franrobots/RescueMaze_FranRobots_National2024/Mechanics/MAZE ROBOT 2024/Extras/Render/Renders antigas/Configurações Render.jpg

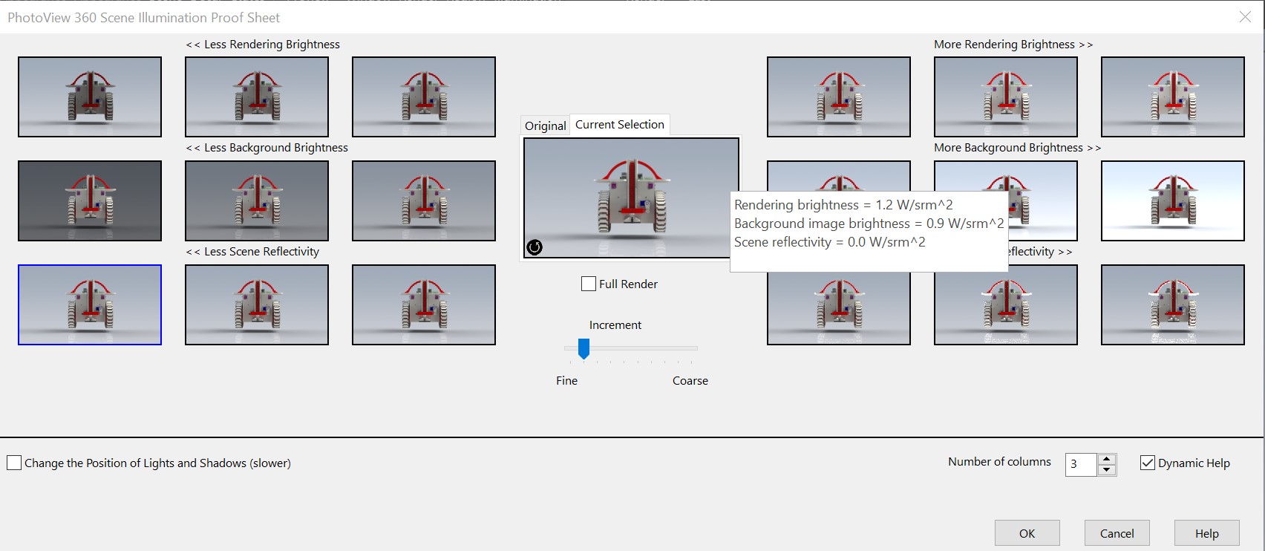
Mechanics/MAZE ROBOT 2024/Extras/Render/Renders antigas/Configurações Render.jpg
