franrobots/RescueMaze_FranRobots_National2024/Programming/Media/Flowcharts/Fluxograma Botão de Interrupção.png

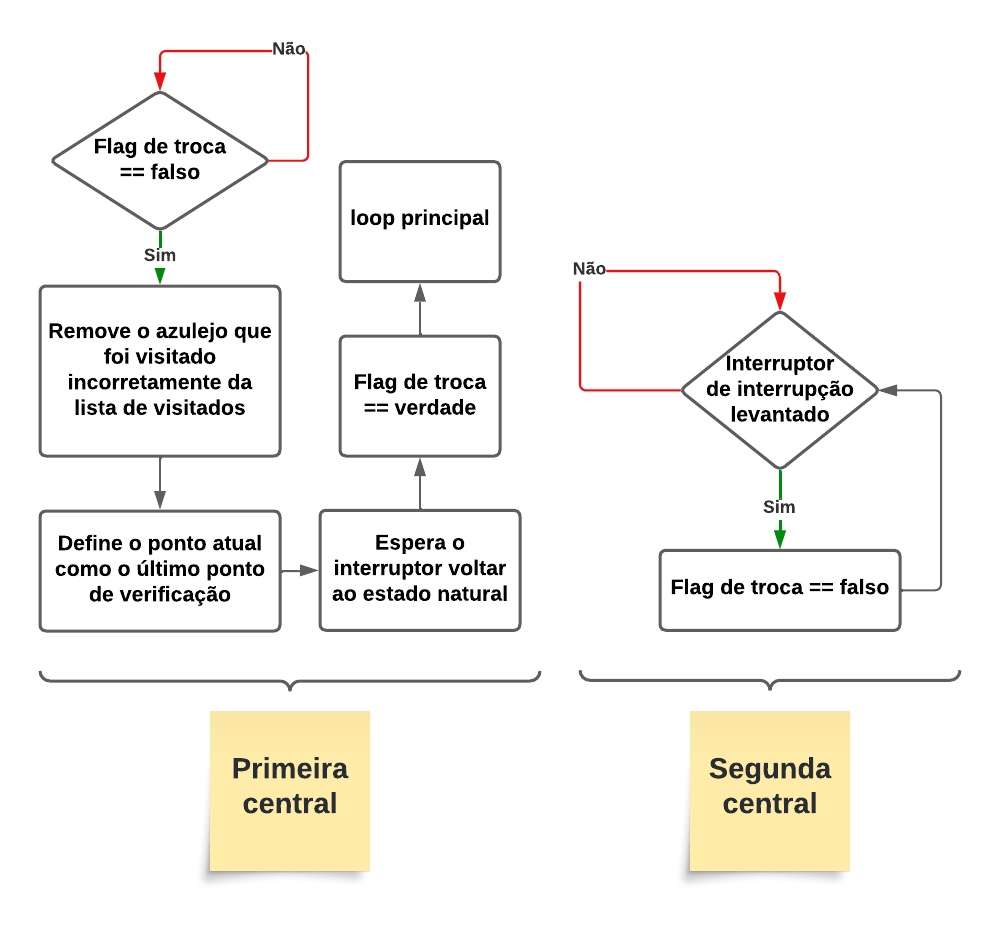
Programming/Media/Flowcharts/Fluxograma Botão de Interrupção.png
