franrobots/RescueMaze_FranRobots_National2024/Programming/Media/Flowcharts/Fluxograma Decisões do Robô.png

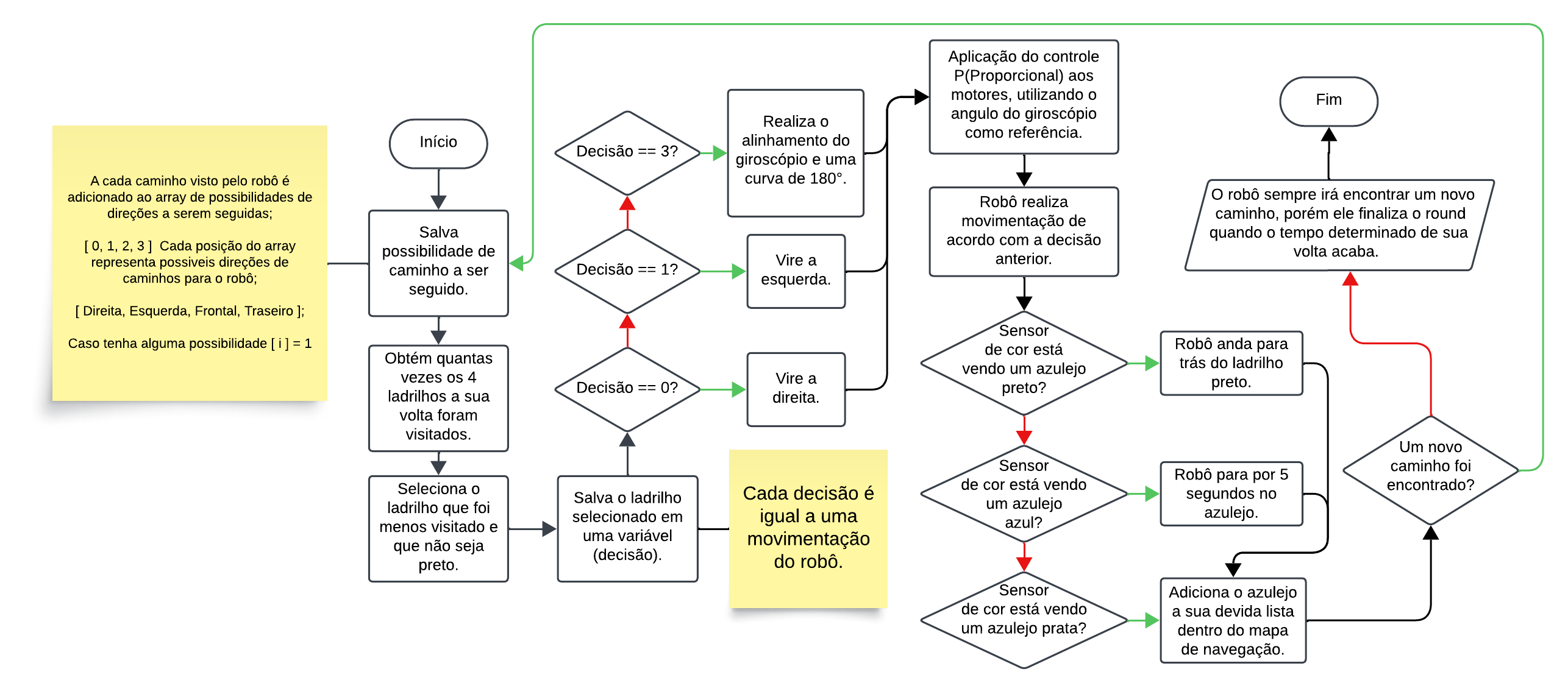
Programming/Media/Flowcharts/Fluxograma Decisões do Robô.png
