franrobots/RescueMaze_FranRobots_National2024/Programming/Media/Flowcharts/Fluxograma Identificação de Imagem.png

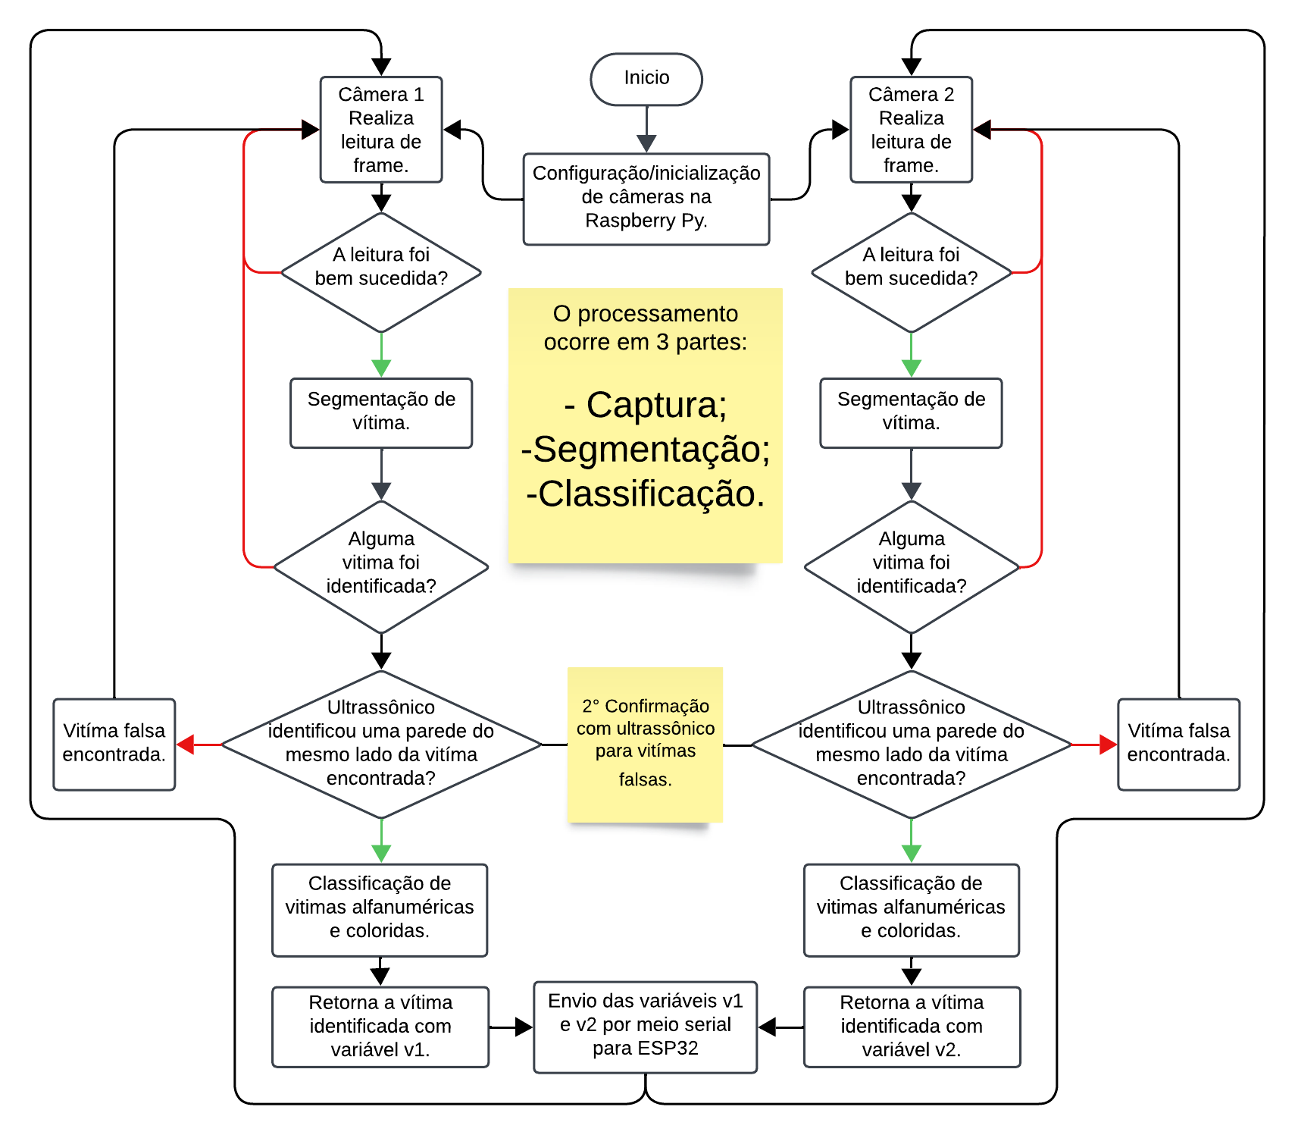
Programming/Media/Flowcharts/Fluxograma Identificação de Imagem.png
