franrobots/RescueMaze_FranRobots_National2024/Programming/Media/Flowcharts/Fluxograma Ladrilhos Coloridos.png

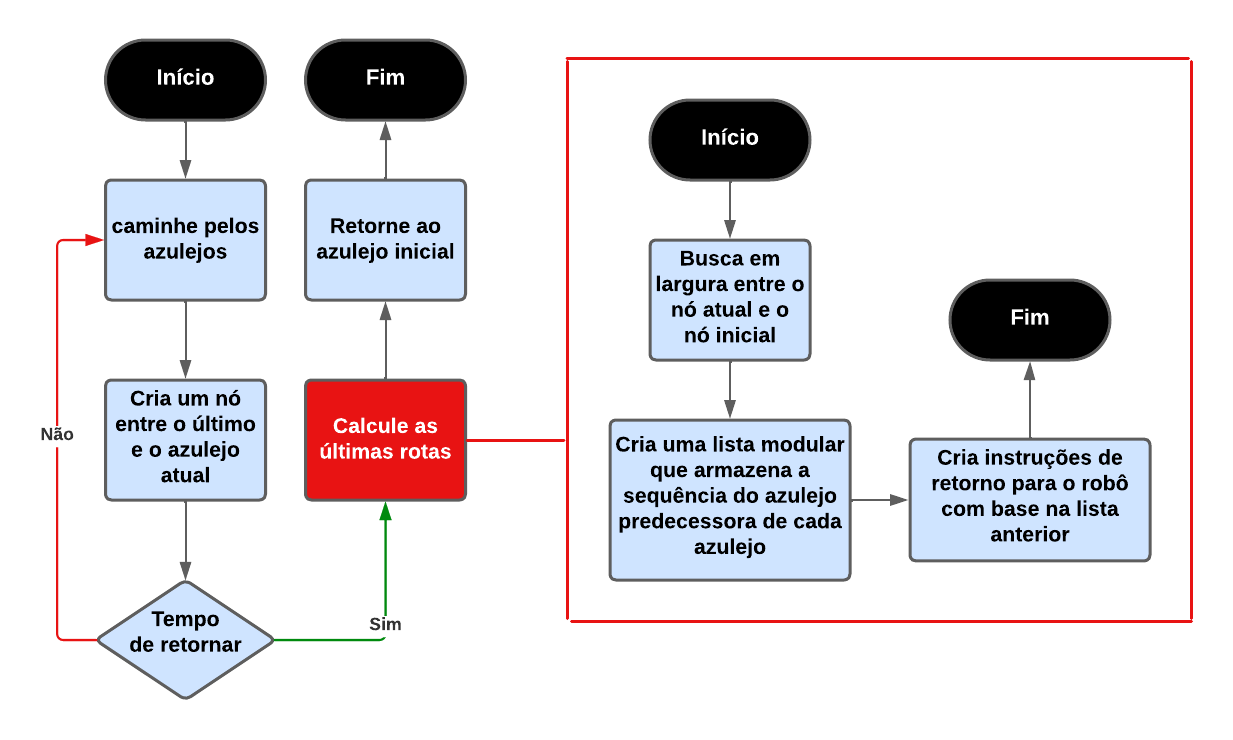
Programming/Media/Flowcharts/Fluxograma Ladrilhos Coloridos.png
