franrobots/RescueMaze_FranRobots_National2024/Programming/Media/Flowcharts/Fluxograma LDR.png

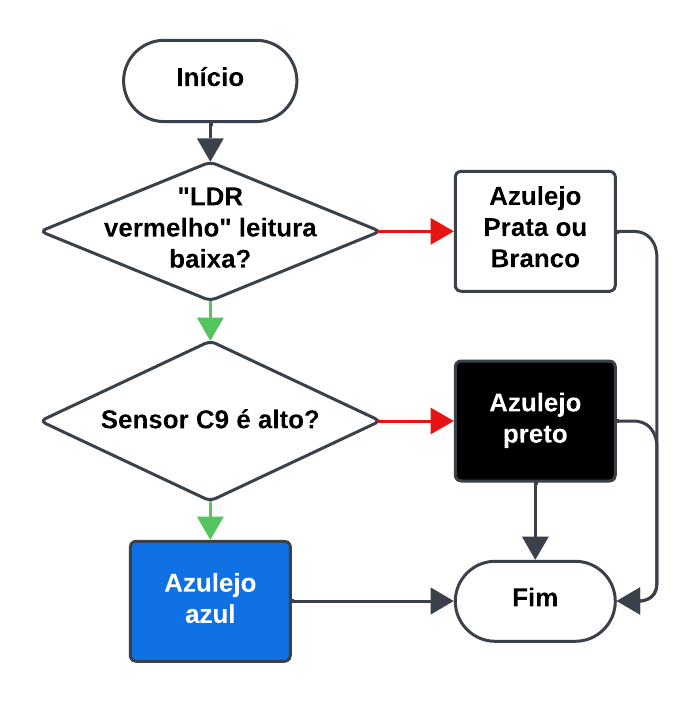
Programming/Media/Flowcharts/Fluxograma LDR.png
