franrobots/RescueMaze_FranRobots_National2024/Programming/Media/Flowcharts/Fluxograma Rotas.png

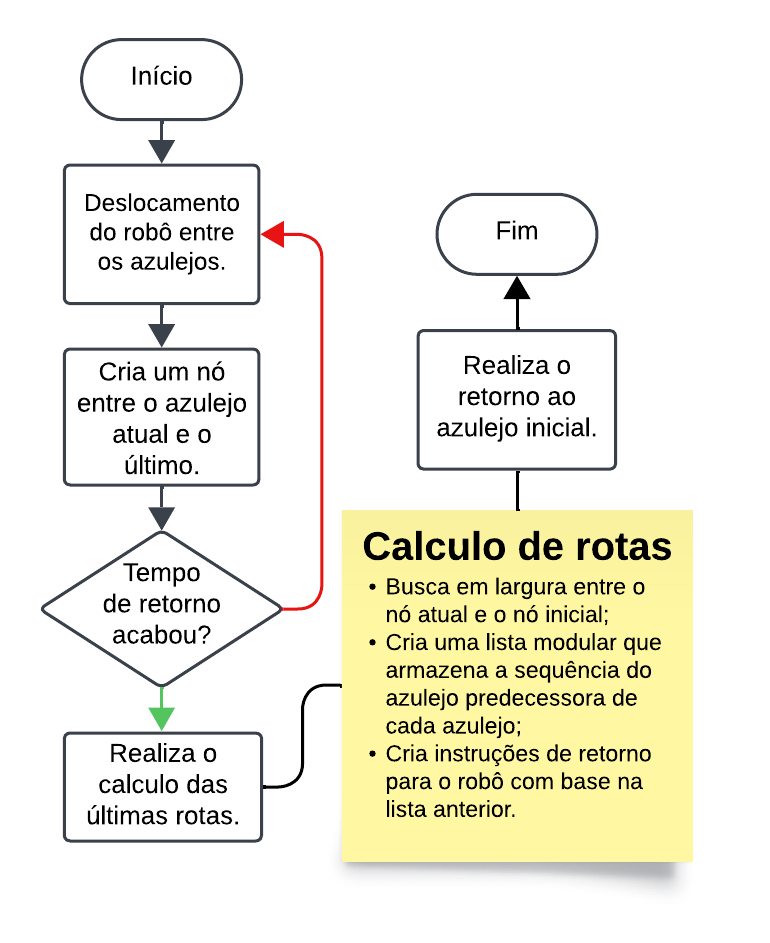
Programming/Media/Flowcharts/Fluxograma Rotas.png
