franrobots/RescueMaze_FranRobots_National2024/Mechanics/MAZE ROBOT 2024/Componentes/Micro-controladoras/RaspberryPi Zero/RaspberryPiZeroW.SLDPRT

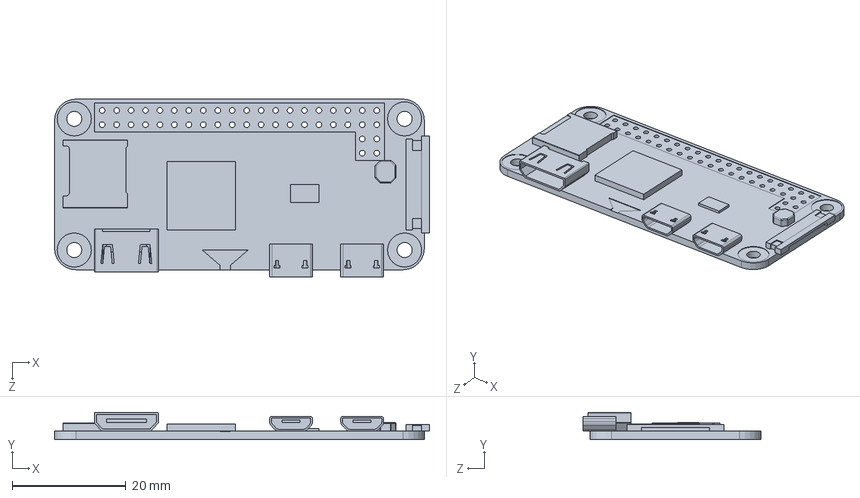
[picture p37: CAD file, 2024-10-25]
Mechanics/MAZE ROBOT 2024/Componentes/Micro-controladoras/RaspberryPi Zero/RaspberryPiZeroW.SLDPRT
65.9 x 4.80 x 31.2 mm
