franrobots/RescueMaze_FranRobots_National2024/Mechanics/MAZE ROBOT 2024/Componentes/Motor DC - MJ TEK8 - 12v 100 RPM.SLDPRT

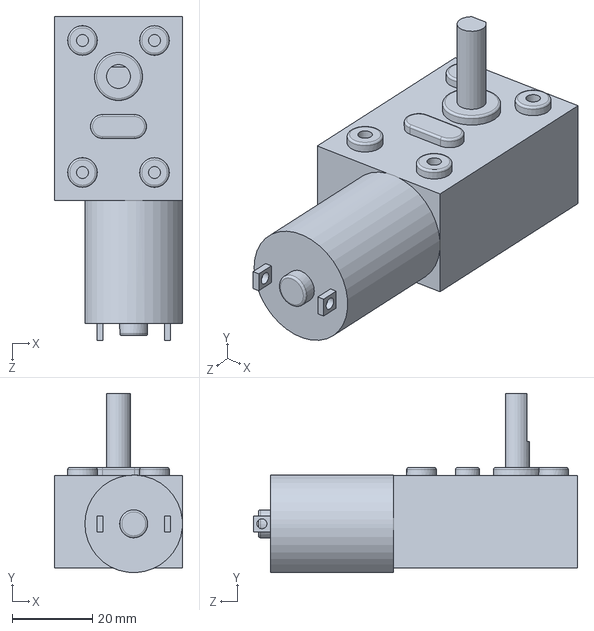
[picture p38: CAD file, 2024-10-25]
Mechanics/MAZE ROBOT 2024/Componentes/Motor DC - MJ TEK8 - 12v 100 RPM.SLDPRT
32.0 x 44.8 x 81.0 mm
