franrobots/RescueMaze_FranRobots_National2024/Mechanics/MAZE ROBOT 2024/Componentes/Parafusos e Porcas/Arruelas/Arruela M3.SLDPRT

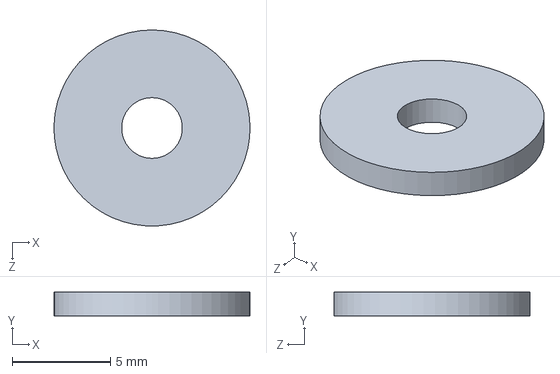
[picture p39: CAD file, 2024-10-25]
Mechanics/MAZE ROBOT 2024/Componentes/Parafusos e Porcas/Arruelas/Arruela M3.SLDPRT
10.00 x 1.20 x 10.0 mm
