franrobots/RescueMaze_FranRobots_National2024/Mechanics/MAZE ROBOT 2024/Componentes/Parafusos e Porcas/Parafusos/Parafuso M3 Liso.SLDPRT

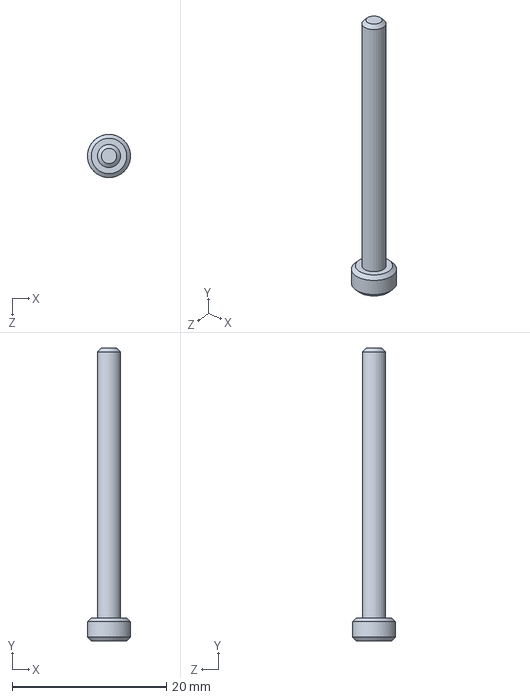
[picture p40: CAD file, 2024-10-25]
Mechanics/MAZE ROBOT 2024/Componentes/Parafusos e Porcas/Parafusos/Parafuso M3 Liso.SLDPRT
5.59 x 38.0 x 5.60 mm
