franrobots/RescueMaze_FranRobots_National2024/Mechanics/MAZE ROBOT 2024/Componentes/Parafusos e Porcas/Porcas/Porca M3.STEP

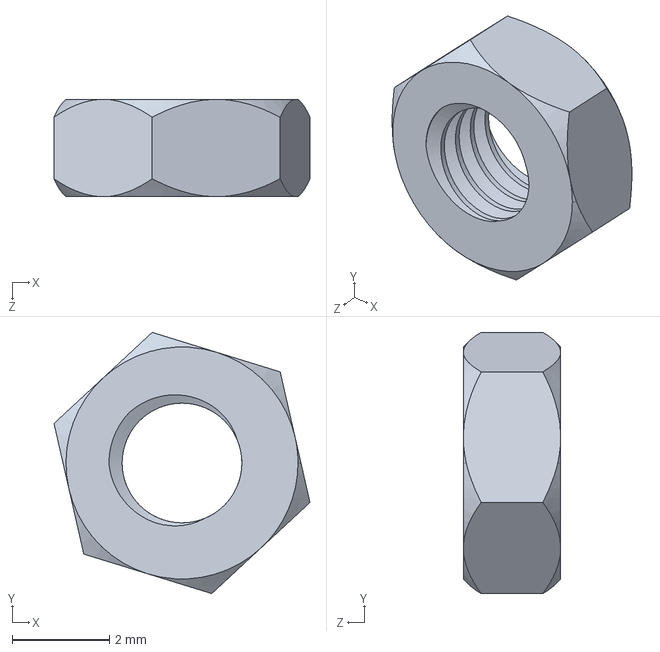
[picture p41: CAD file, 2024-10-25]
Mechanics/MAZE ROBOT 2024/Componentes/Parafusos e Porcas/Porcas/Porca M3.STEP
5.26 x 5.36 x 2.00 mm
