franrobots/RescueMaze_FranRobots_National2024/Mechanics/MAZE ROBOT 2024/Componentes/Placa de Refletância/Case LDR Tripla.SLDPRT

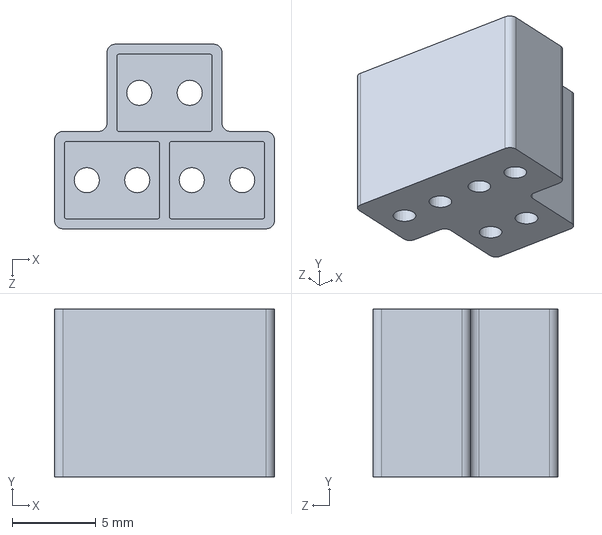
[picture p42: CAD file, 2024-10-25]
Mechanics/MAZE ROBOT 2024/Componentes/Placa de Refletância/Case LDR Tripla.SLDPRT
13.1 x 10.0 x 11.0 mm
