franrobots/RescueMaze_FranRobots_National2024/Mechanics/MAZE ROBOT 2024/Componentes/Placa Mãe - Robô Maze/Conectores/Bornes/2 PIN - DG306-5 - PITCH 5 mm.stp

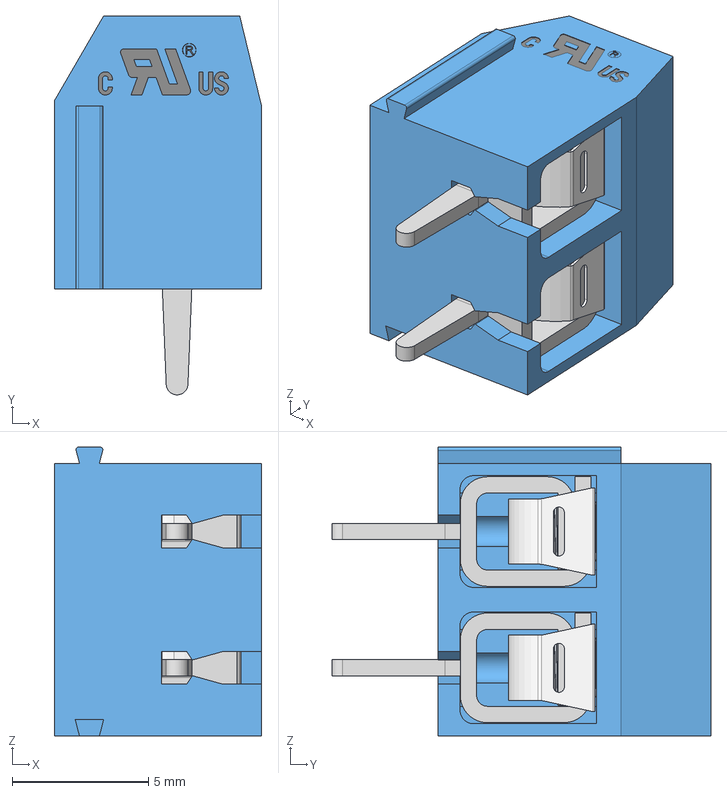
[picture p46: CAD file, 2024-10-25]
Mechanics/MAZE ROBOT 2024/Componentes/Placa Mãe - Robô Maze/Conectores/Bornes/2 PIN - DG306-5 - PITCH 5 mm.stp
7.60 x 13.9 x 10.6 mm
