franrobots/RescueMaze_FranRobots_National2024/Mechanics/MAZE ROBOT 2024/Componentes/Placa Mãe - Robô Maze/Placa Ilhada 90x70.SLDPRT

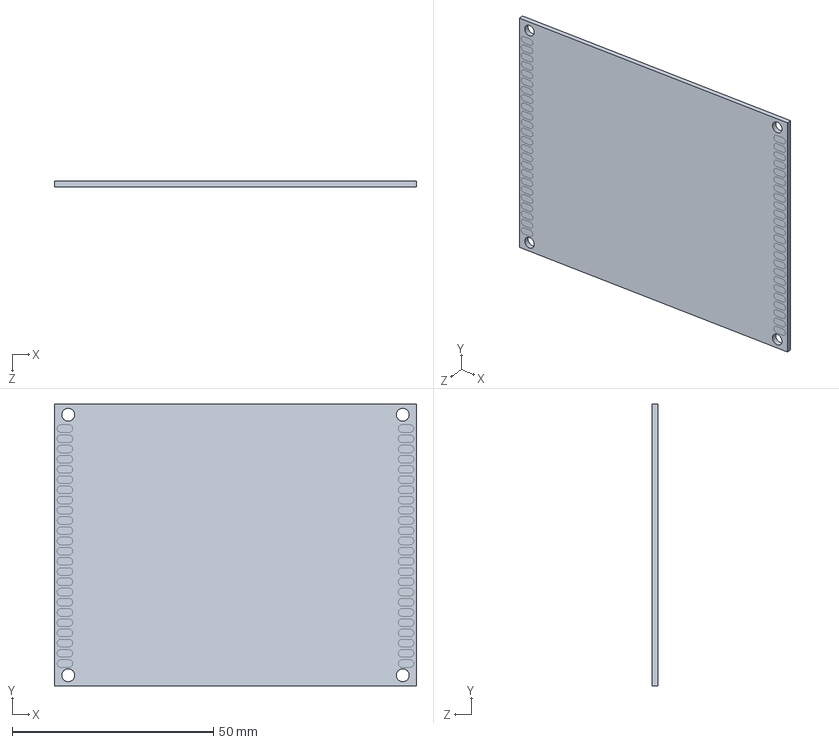
[picture p47: CAD file, 2024-10-25]
Mechanics/MAZE ROBOT 2024/Componentes/Placa Mãe - Robô Maze/Placa Ilhada 90x70.SLDPRT
90.0 x 70.0 x 1.42 mm
