franrobots/RescueMaze_FranRobots_National2024/Mechanics/MAZE ROBOT 2024/Componentes/Servo Motor/Servo Emax ES08A.SLDPRT

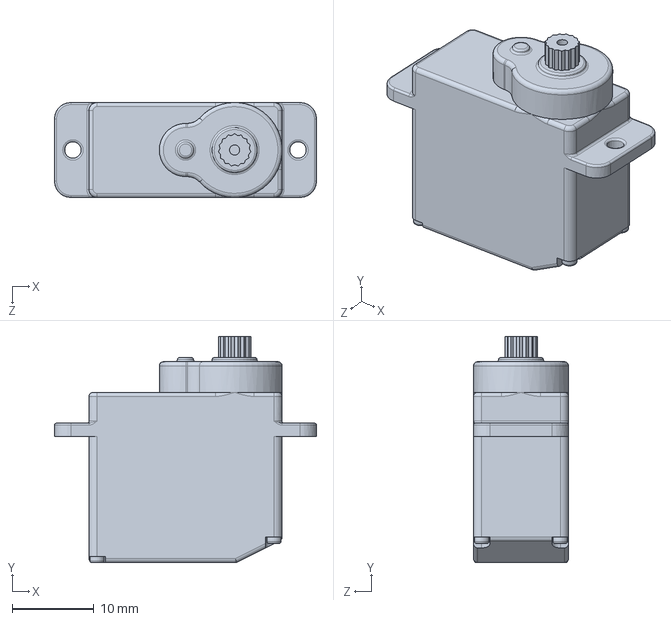
[picture p48: CAD file, 2024-10-25]
Mechanics/MAZE ROBOT 2024/Componentes/Servo Motor/Servo Emax ES08A.SLDPRT
32.0 x 27.6 x 11.6 mm
