franrobots/RescueMaze_FranRobots_National2024/Mechanics/MAZE ROBOT 2024/Componentes/Switchs/3D/Suporte Switch.SLDPRT

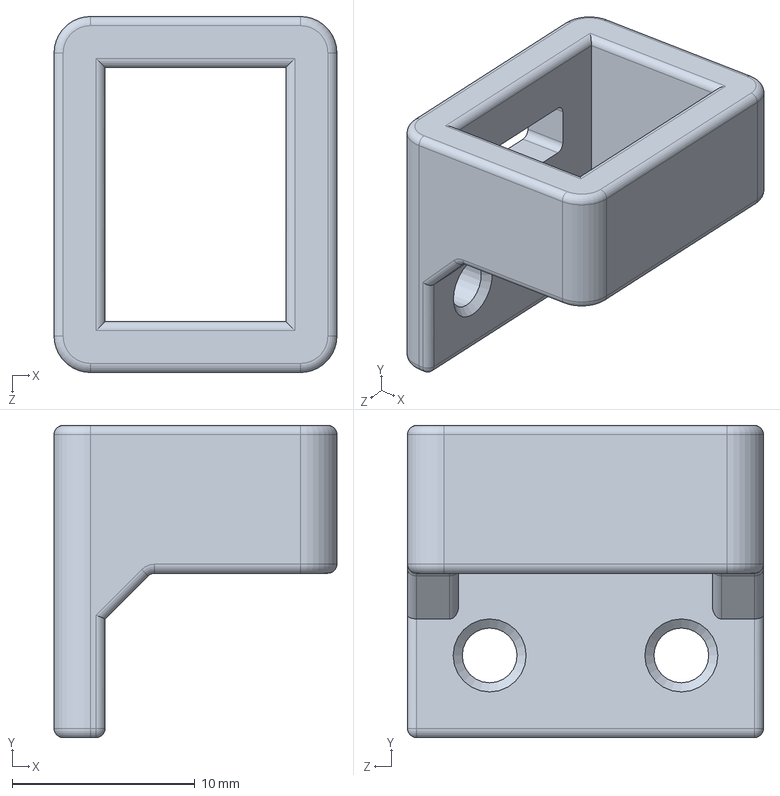
[picture p49: CAD file, 2024-10-25]
Mechanics/MAZE ROBOT 2024/Componentes/Switchs/3D/Suporte Switch.SLDPRT
15.5 x 17.1 x 19.5 mm
