franrobots/RescueMaze_FranRobots_National2024/Mechanics/MAZE ROBOT 2024/Componentes/Switchs/tugas uts rocker switch.SLDPRT

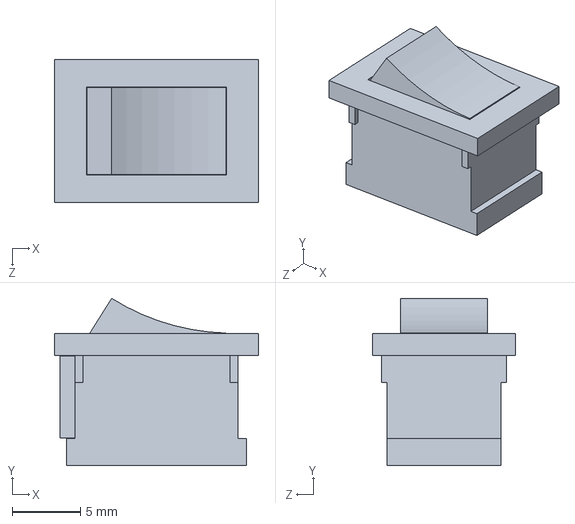
[picture p50: CAD file, 2024-10-25]
Mechanics/MAZE ROBOT 2024/Componentes/Switchs/tugas uts rocker switch.SLDPRT
15.0 x 12.3 x 10.5 mm
