franrobots/RescueMaze_FranRobots_National2024/Mechanics/MAZE ROBOT 2024/Componentes/Ultrassonico/Suporte Ultrassonico.SLDPRT

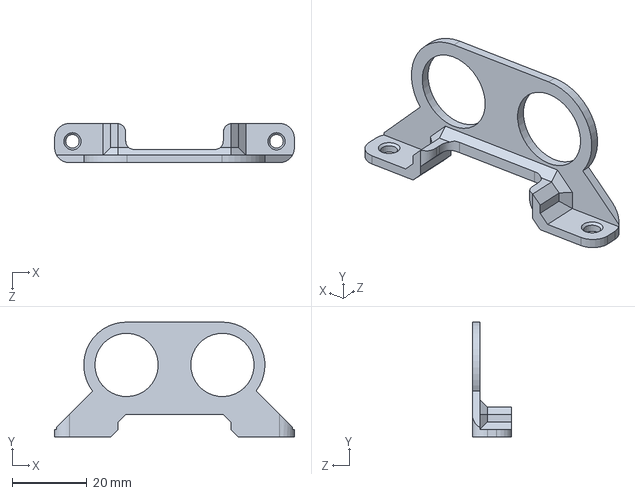
[picture p51: CAD file, 2024-10-25]
Mechanics/MAZE ROBOT 2024/Componentes/Ultrassonico/Suporte Ultrassonico.SLDPRT
64.1 x 30.7 x 10.5 mm
