franrobots/RescueMaze_FranRobots_National2024/Mechanics/MAZE ROBOT 2024/Disparador/Disparador Tapete/Conector Servo Manivela.SLDPRT

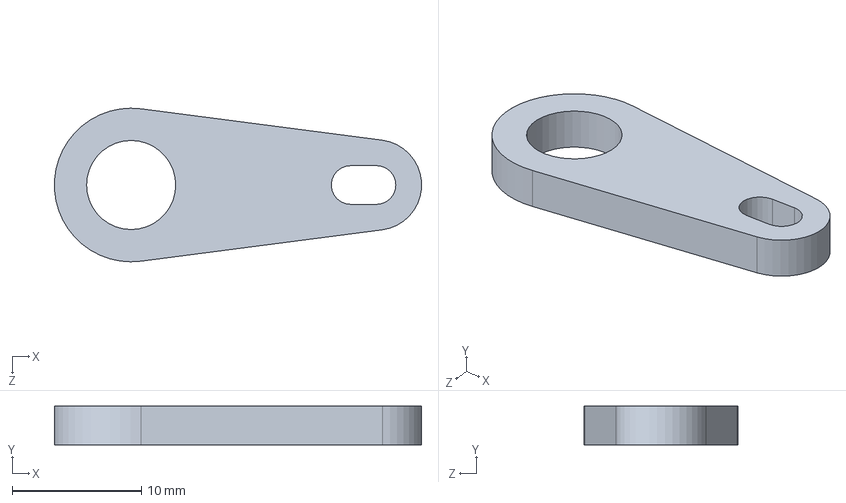
[picture p52: CAD file, 2024-10-25]
Mechanics/MAZE ROBOT 2024/Disparador/Disparador Tapete/Conector Servo Manivela.SLDPRT
28.4 x 3.00 x 11.9 mm
