franrobots/RescueMaze_FranRobots_National2024/Mechanics/MAZE ROBOT 2024/Disparador/Estoque Disparador/Parede - Estoque Disparador.SLDPRT

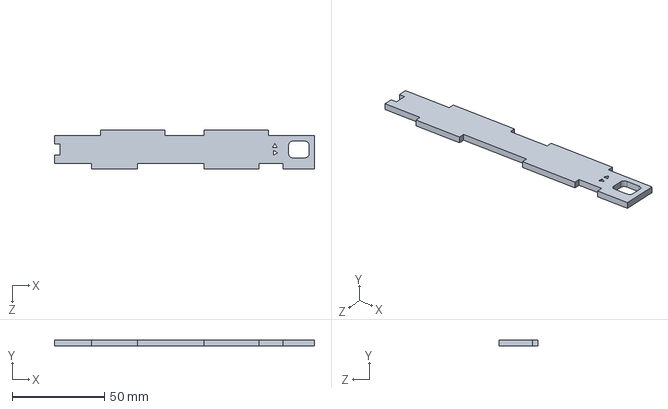
[picture p53: CAD file, 2024-10-25]
Mechanics/MAZE ROBOT 2024/Disparador/Estoque Disparador/Parede - Estoque Disparador.SLDPRT
141.0 x 3.00 x 21.0 mm
