franrobots/RescueMaze_FranRobots_National2024/Mechanics/MAZE ROBOT 2024/Disparador/Tampa Disparador.SLDPRT

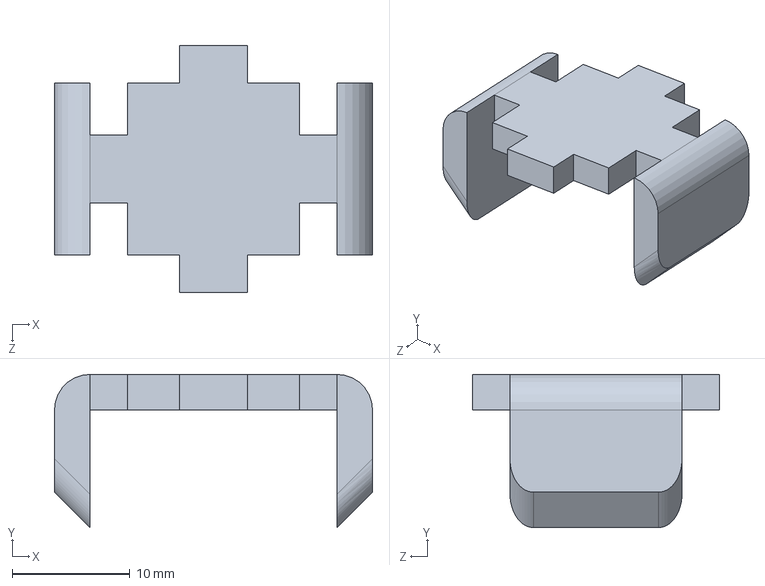
[picture p54: CAD file, 2024-10-25]
Mechanics/MAZE ROBOT 2024/Disparador/Tampa Disparador.SLDPRT
27.0 x 13.0 x 21.0 mm
