franrobots/RescueMaze_FranRobots_National2024/Mechanics/MAZE ROBOT 2024/Extras/Adereços/Chifre.SLDPRT

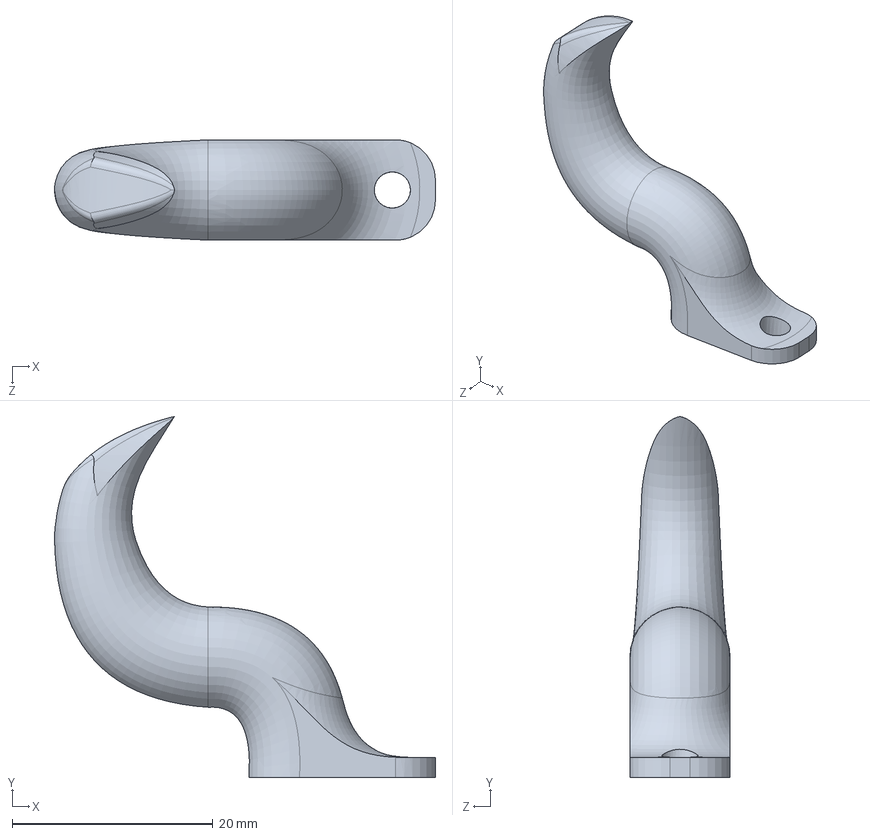
[picture p55: CAD file, 2024-10-25]
Mechanics/MAZE ROBOT 2024/Extras/Adereços/Chifre.SLDPRT
38.0 x 36.0 x 10.0 mm
