franrobots/RescueMaze_FranRobots_National2024/Mechanics/MAZE ROBOT 2024/Extras/Logos/DXF/Bandeira do Brasil.dxf

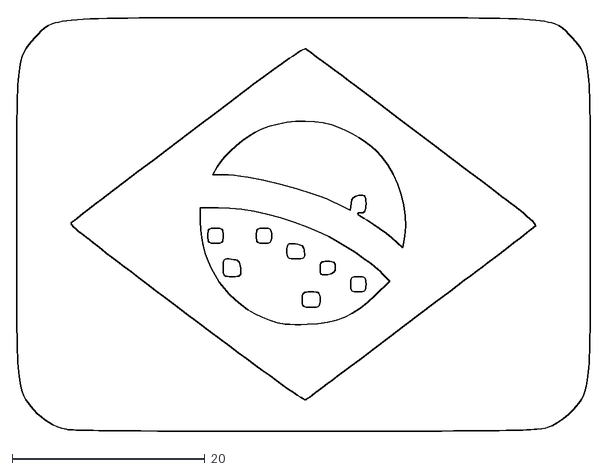
[picture p56: CAD file, 2024-10-25]
Mechanics/MAZE ROBOT 2024/Extras/Logos/DXF/Bandeira do Brasil.dxf
59.6 x 43.1
