franrobots/RescueMaze_FranRobots_National2024/Mechanics/MAZE ROBOT 2024/Peças Frente/Peça Frente Baixo - Maze.SLDPRT

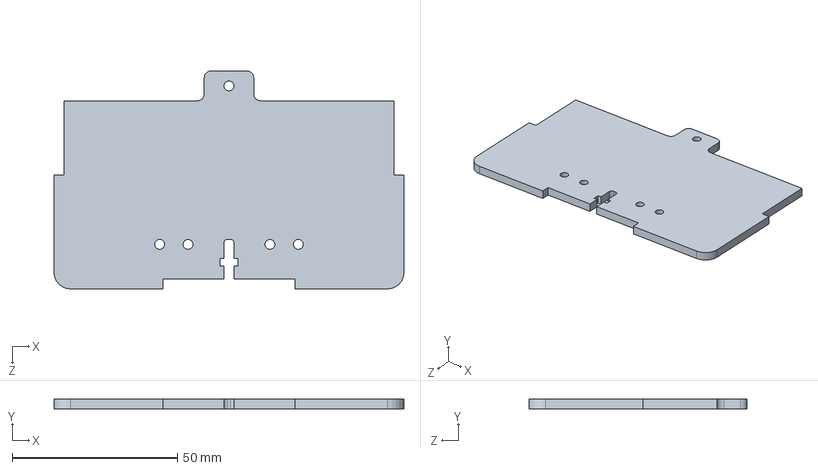
[picture p57: CAD file, 2024-10-25]
Mechanics/MAZE ROBOT 2024/Peças Frente/Peça Frente Baixo - Maze.SLDPRT
106.0 x 3.00 x 66.0 mm
