franrobots/RescueMaze_FranRobots_National2024/Mechanics/MAZE ROBOT 2024/Pista/Redutor.SLDPRT

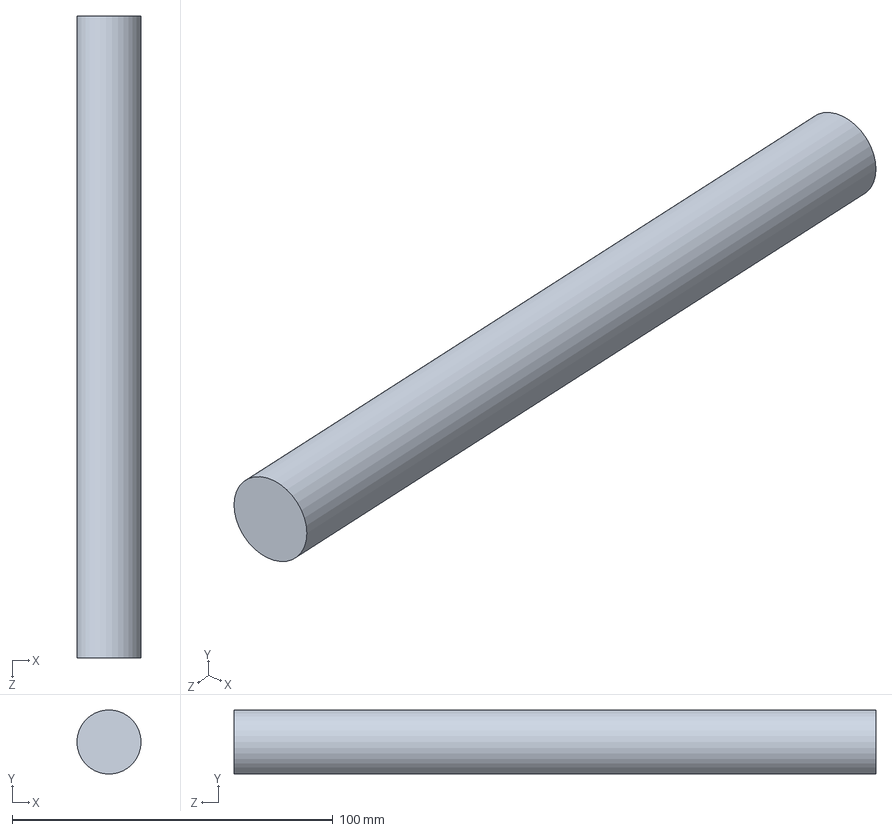
[picture p58: CAD file, 2024-10-25]
Mechanics/MAZE ROBOT 2024/Pista/Redutor.SLDPRT
20.0 x 19.9 x 200.0 mm
