franrobots/RescueMaze_FranRobots_National2024/Mechanics/MAZE ROBOT 2024/Bumper/Peça AntiCapotamento.SLDPRT

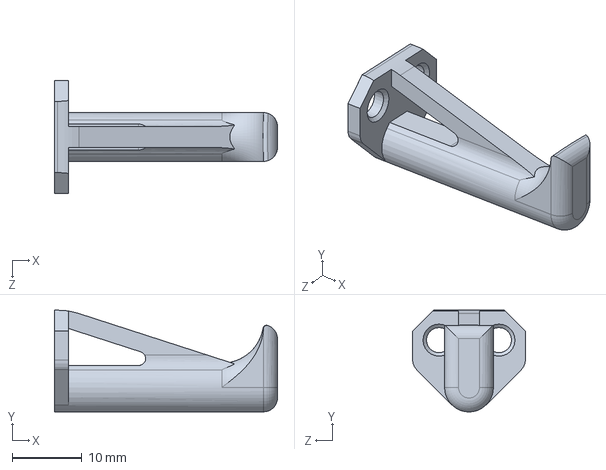
[picture p60: CAD file, 2024-10-25]
Mechanics/MAZE ROBOT 2024/Bumper/Peça AntiCapotamento.SLDPRT
32.0 x 14.6 x 16.2 mm
