franrobots/RescueMaze_FranRobots_National2024/Mechanics/MAZE ROBOT 2024/Bumper/Switch Bumper/SwitchBumper Meio.SLDPRT

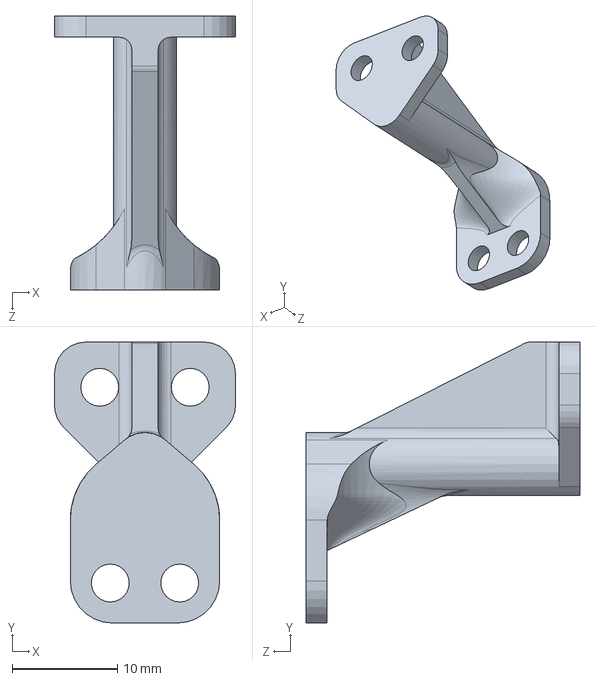
[picture p61: CAD file, 2024-10-25]
Mechanics/MAZE ROBOT 2024/Bumper/Switch Bumper/SwitchBumper Meio.SLDPRT
17.2 x 26.7 x 26.0 mm
