franrobots/RescueMaze_FranRobots_National2024/Mechanics/MAZE ROBOT 2024/Componentes/Bateria/Leão Battery LiPo 3S 2.2Ah 11.1V.SLDPRT

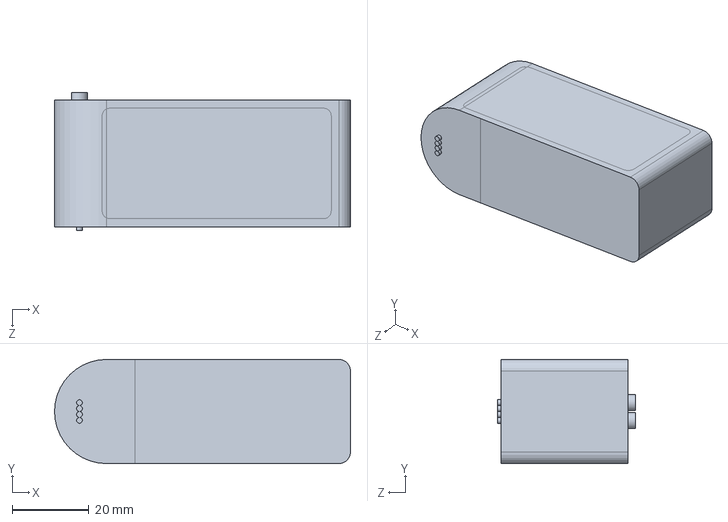
[picture p62: CAD file, 2024-10-25]
Mechanics/MAZE ROBOT 2024/Componentes/Bateria/Leão Battery LiPo 3S 2.2Ah 11.1V.SLDPRT
77.0 x 27.1 x 36.0 mm
