franrobots/RescueMaze_FranRobots_National2024/Mechanics/MAZE ROBOT 2024/Componentes/Câmera/Câmera Genérica.SLDPRT

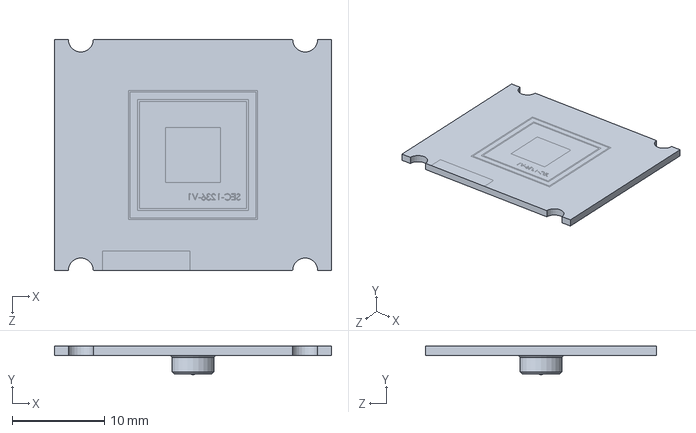
[picture p63: CAD file, 2024-10-25]
Mechanics/MAZE ROBOT 2024/Componentes/Câmera/Câmera Genérica.SLDPRT
30.0 x 3.10 x 25.0 mm
