franrobots/RescueMaze_FranRobots_National2024/Mechanics/MAZE ROBOT 2024/Componentes/Encoder/Encoder Mod/Encoder Motor Mod..SLDPRT

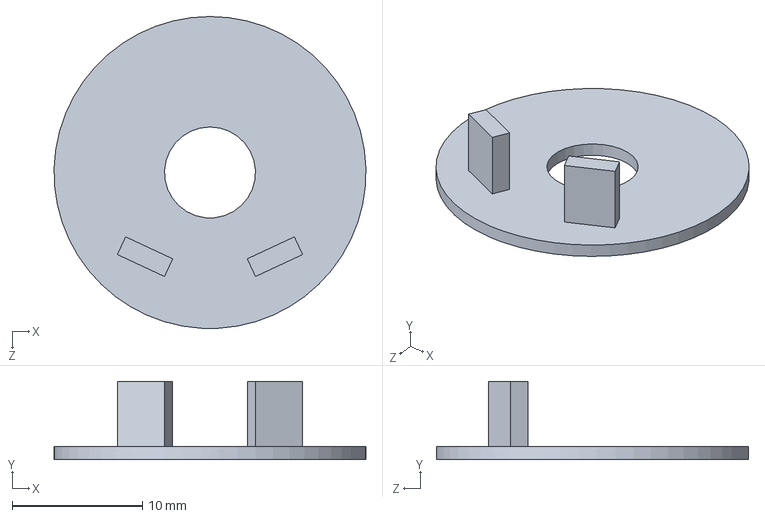
[picture p64: CAD file, 2024-10-25]
Mechanics/MAZE ROBOT 2024/Componentes/Encoder/Encoder Mod/Encoder Motor Mod..SLDPRT
24.0 x 6.00 x 24.0 mm
