franrobots/RescueMaze_FranRobots_National2024/Mechanics/MAZE ROBOT 2024/Componentes/GY-VL53/GY-VL53L0XV2.SLDPRT

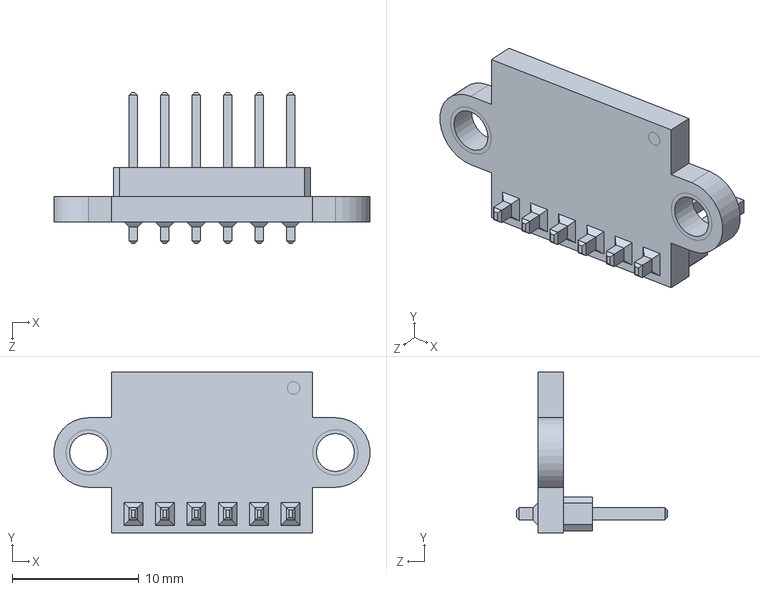
[picture p65: CAD file, 2024-10-25]
Mechanics/MAZE ROBOT 2024/Componentes/GY-VL53/GY-VL53L0XV2.SLDPRT
25.0 x 12.7 x 11.9 mm
