franrobots/RescueMaze_FranRobots_National2024/Mechanics/MAZE ROBOT 2024/Componentes/L298N Motor Driver.SLDPRT

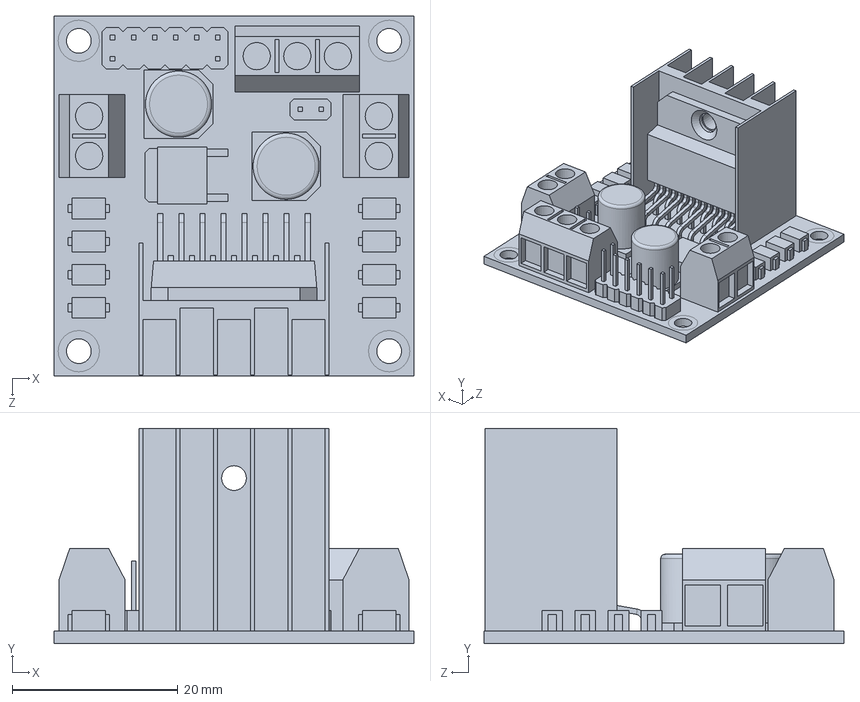
[picture p66: CAD file, 2024-10-25]
Mechanics/MAZE ROBOT 2024/Componentes/L298N Motor Driver.SLDPRT
43.5 x 26.0 x 43.5 mm
