franrobots/RescueMaze_FranRobots_National2024/Mechanics/MAZE ROBOT 2024/Componentes/Parafusos e Porcas/Arruelas/Arruela M4.SLDPRT

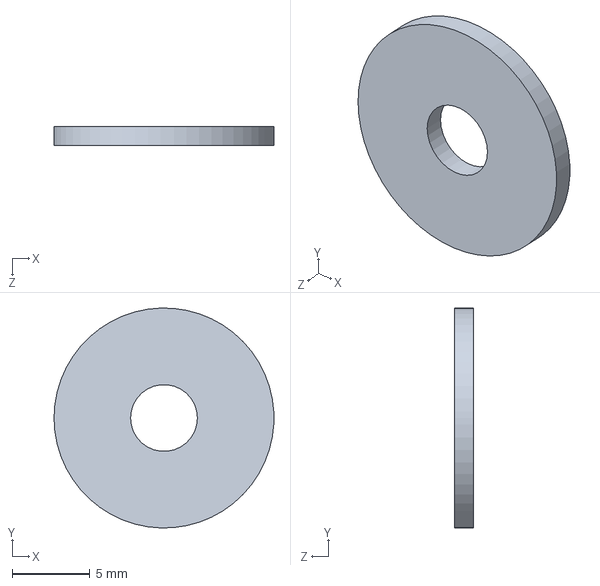
[picture p67: CAD file, 2024-10-25]
Mechanics/MAZE ROBOT 2024/Componentes/Parafusos e Porcas/Arruelas/Arruela M4.SLDPRT
14.2 x 14.2 x 1.22 mm
