franrobots/RescueMaze_FranRobots_National2024/Mechanics/MAZE ROBOT 2024/Componentes/Parafusos e Porcas/Parafusos/Parafuso M3 Fuso.SLDPRT

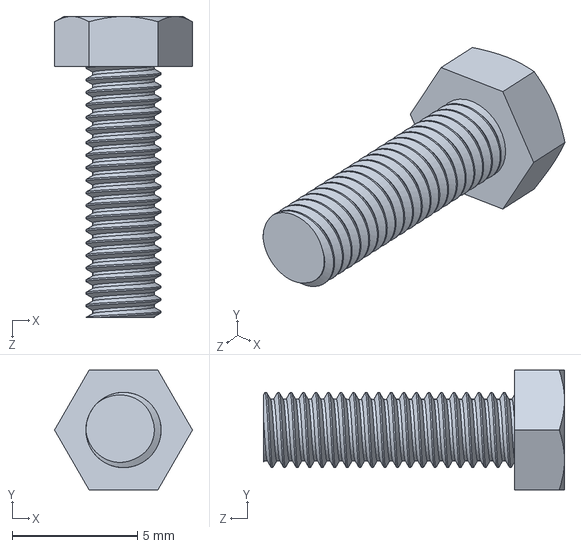
[picture p68: CAD file, 2024-10-25]
Mechanics/MAZE ROBOT 2024/Componentes/Parafusos e Porcas/Parafusos/Parafuso M3 Fuso.SLDPRT
5.50 x 4.76 x 12.0 mm
