franrobots/RescueMaze_FranRobots_National2024/Mechanics/MAZE ROBOT 2024/Componentes/Parafusos e Porcas/Porcas/Porca M4.stp

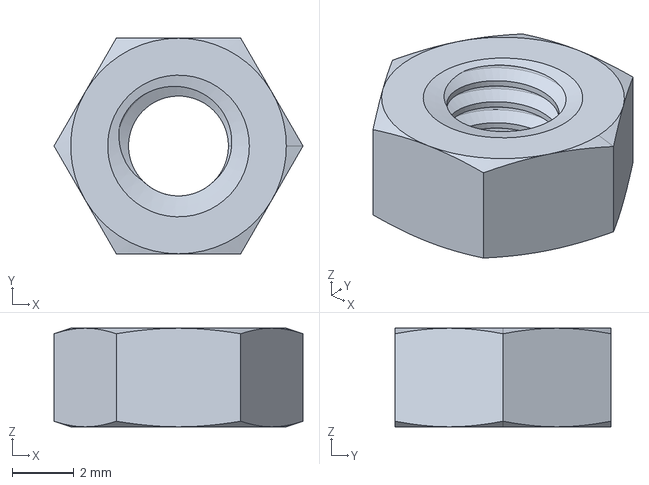
[picture p69: CAD file, 2024-10-25]
Mechanics/MAZE ROBOT 2024/Componentes/Parafusos e Porcas/Porcas/Porca M4.stp
8.08 x 7.00 x 3.20 mm
