franrobots/RescueMaze_FranRobots_National2024/Mechanics/MAZE ROBOT 2024/Componentes/Placa de Refletância/Case LDR Sobrepor.SLDPRT

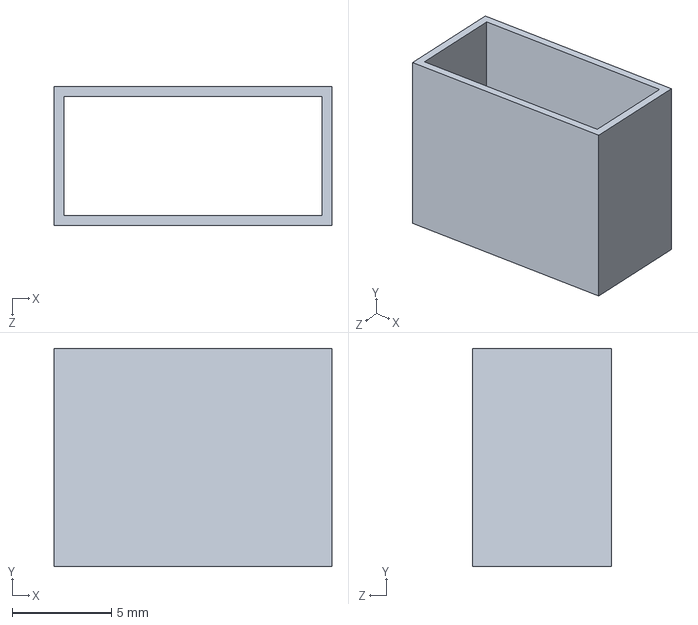
[picture p70: CAD file, 2024-10-25]
Mechanics/MAZE ROBOT 2024/Componentes/Placa de Refletância/Case LDR Sobrepor.SLDPRT
14.0 x 11.0 x 7.00 mm
