franrobots/RescueMaze_FranRobots_National2024/Mechanics/MAZE ROBOT 2024/Componentes/Placa Mãe - Robô Maze/Conectores/Barras Pinada Fêmea/19-Pin Header - Female - 2.54mm.STEP

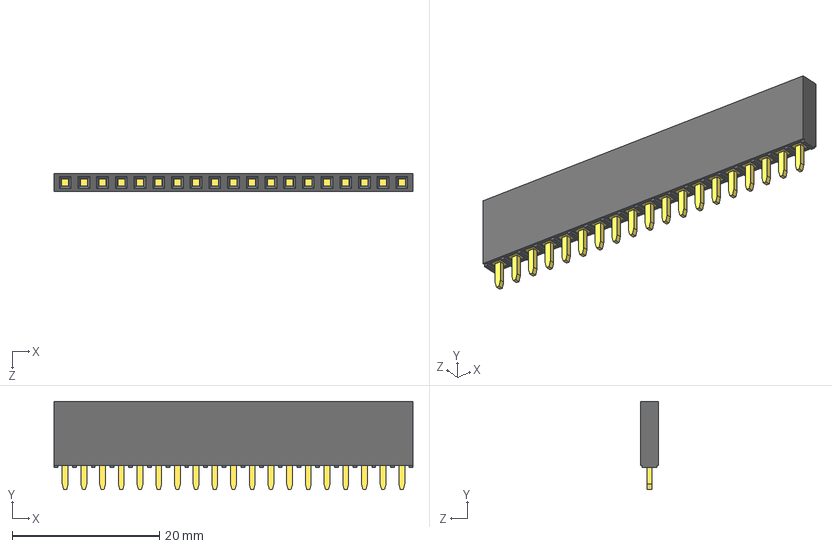
[picture p71: CAD file, 2024-10-25]
Mechanics/MAZE ROBOT 2024/Componentes/Placa Mãe - Robô Maze/Conectores/Barras Pinada Fêmea/19-Pin Header - Female - 2.54mm.STEP
48.8 x 12.0 x 2.50 mm
