franrobots/RescueMaze_FranRobots_National2024/Mechanics/MAZE ROBOT 2024/Componentes/Placa Mãe - Robô Maze/Conectores/Barras Pinada Macho/1-Pin Header - Male - 2.54mm/1-Pin Header (Without Limit)- Male - 2.54mm.STEP

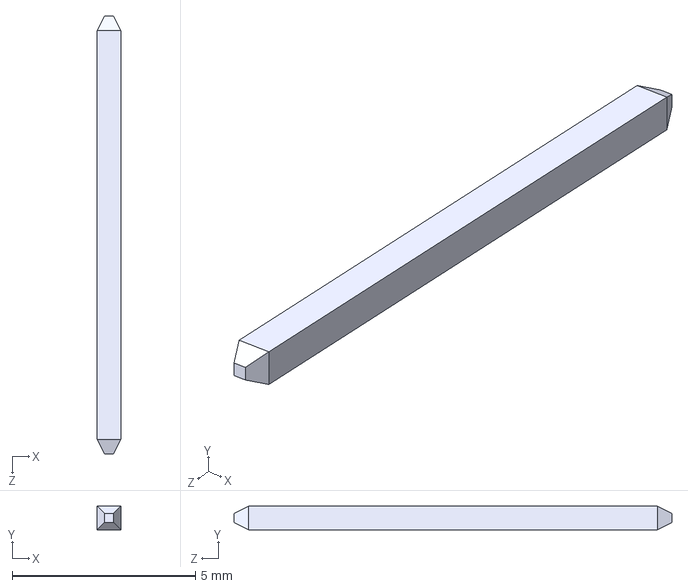
[picture p72: CAD file, 2024-10-25]
Mechanics/MAZE ROBOT 2024/Componentes/Placa Mãe - Robô Maze/Conectores/Barras Pinada Macho/1-Pin Header - Male - 2.54mm/1-Pin Header (Without Limit)- Male - 2.54mm.STEP
0.65 x 0.65 x 11.9 mm
