franrobots/RescueMaze_FranRobots_National2024/Mechanics/MAZE ROBOT 2024/Componentes/Servo Motor/Aleta Micro Servo - Tower Pro.SLDPRT

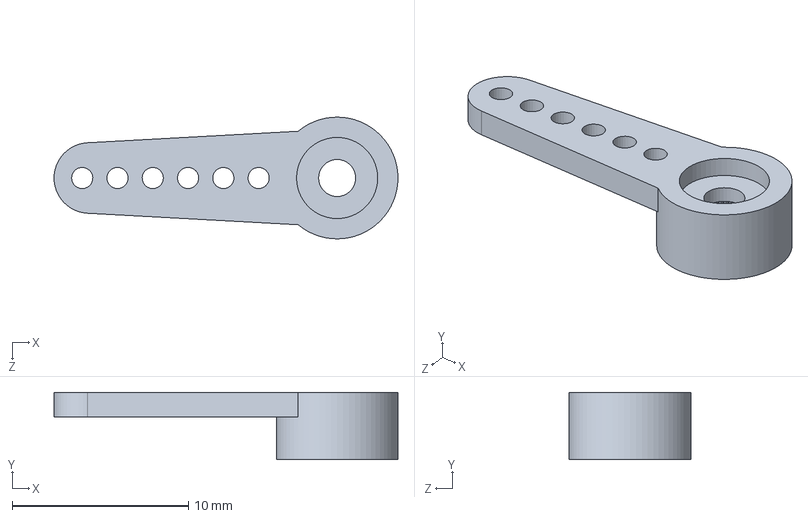
[picture p74: CAD file, 2024-10-25]
Mechanics/MAZE ROBOT 2024/Componentes/Servo Motor/Aleta Micro Servo - Tower Pro.SLDPRT
19.5 x 3.80 x 6.90 mm
