franrobots/RescueMaze_FranRobots_National2024/Mechanics/MAZE ROBOT 2024/Componentes/Switchs/RockerSwitch.SLDPRT

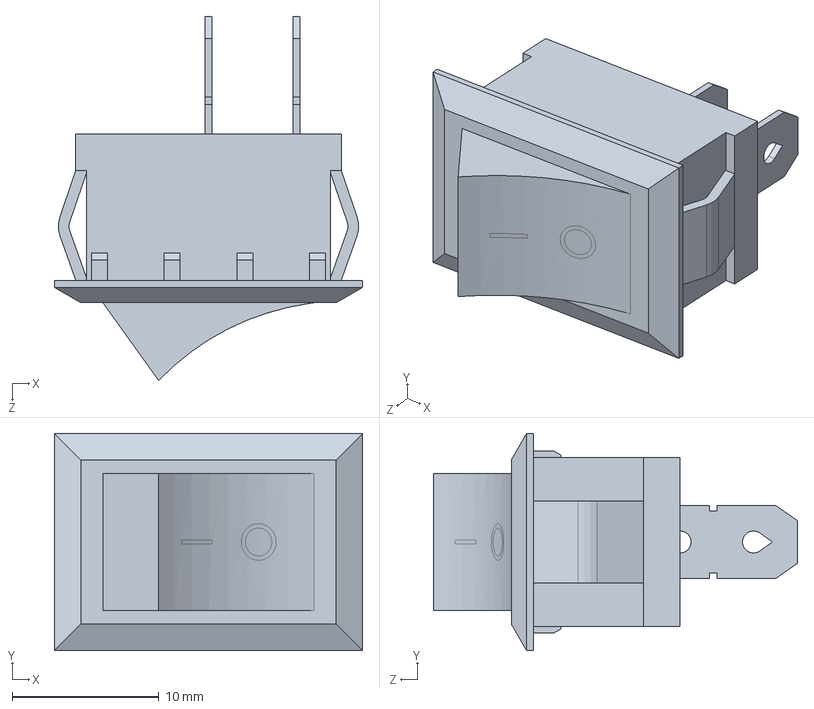
[picture p75: CAD file, 2024-10-25]
Mechanics/MAZE ROBOT 2024/Componentes/Switchs/RockerSwitch.SLDPRT
21.0 x 14.8 x 24.8 mm
