franrobots/RescueMaze_FranRobots_National2024/Mechanics/MAZE ROBOT 2024/Componentes/Ultrassonico/Suporte Ultrassonico Vertical.SLDPRT

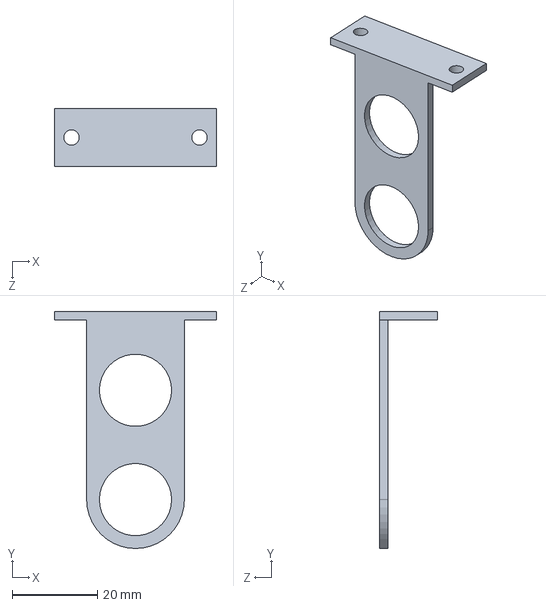
[picture p76: CAD file, 2024-10-25]
Mechanics/MAZE ROBOT 2024/Componentes/Ultrassonico/Suporte Ultrassonico Vertical.SLDPRT
38.0 x 55.5 x 13.6 mm
