franrobots/RescueMaze_FranRobots_National2024/Mechanics/MAZE ROBOT 2024/Disparador/Disparador Tapete/Parede Limite - Disparador.SLDPRT

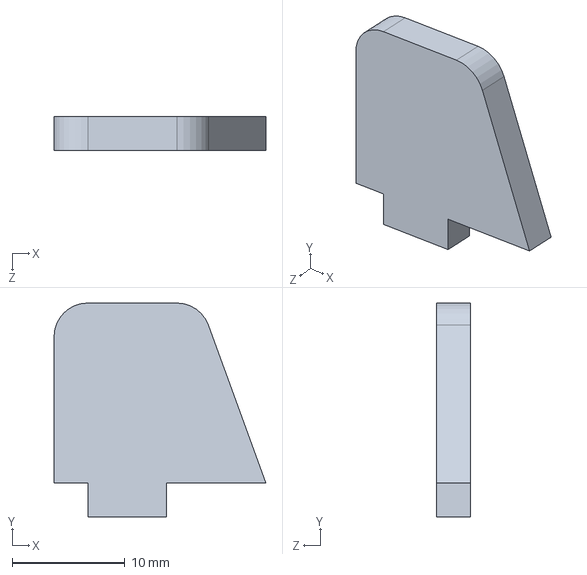
[picture p77: CAD file, 2024-10-25]
Mechanics/MAZE ROBOT 2024/Disparador/Disparador Tapete/Parede Limite - Disparador.SLDPRT
18.8 x 19.0 x 3.00 mm
