franrobots/RescueMaze_FranRobots_National2024/Mechanics/MAZE ROBOT 2024/Disparador/Estoque Disparador/Parede Baixo - Estoque Disparador.SLDPRT

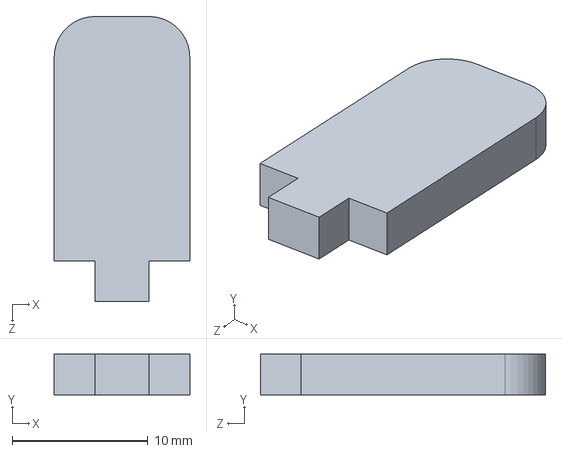
[picture p78: CAD file, 2024-10-25]
Mechanics/MAZE ROBOT 2024/Disparador/Estoque Disparador/Parede Baixo - Estoque Disparador.SLDPRT
10.0 x 3.00 x 21.0 mm
