franrobots/RescueMaze_FranRobots_National2024/Mechanics/MAZE ROBOT 2024/Extras/Logos/DXF/Logo SESI.dxf

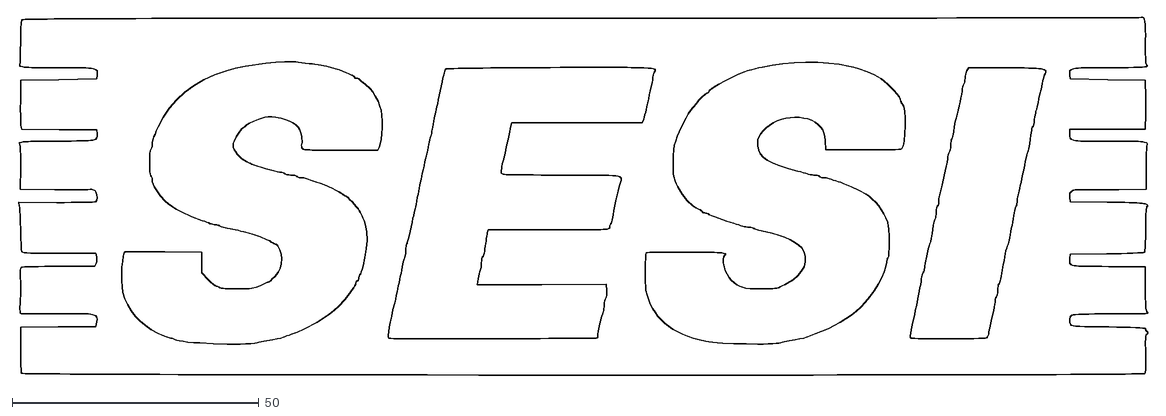
[picture p79: CAD file, 2024-10-25]
Mechanics/MAZE ROBOT 2024/Extras/Logos/DXF/Logo SESI.dxf
229.5 x 72.8
