franrobots/RescueMaze_FranRobots_National2024/Mechanics/MAZE ROBOT 2024/Peças Frente/Peça Frente Cima - Maze.SLDPRT

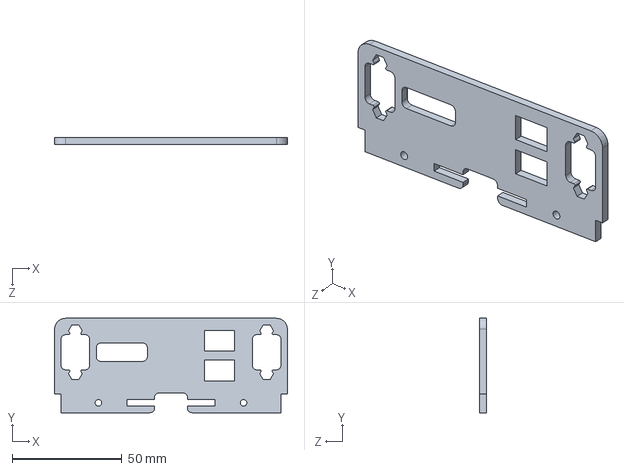
[picture p80: CAD file, 2024-10-25]
Mechanics/MAZE ROBOT 2024/Peças Frente/Peça Frente Cima - Maze.SLDPRT
106.0 x 43.0 x 3.00 mm
