franrobots/RescueMaze_FranRobots_National2024/Mechanics/MAZE ROBOT 2024/Pista/Kit de Resgate.SLDPRT

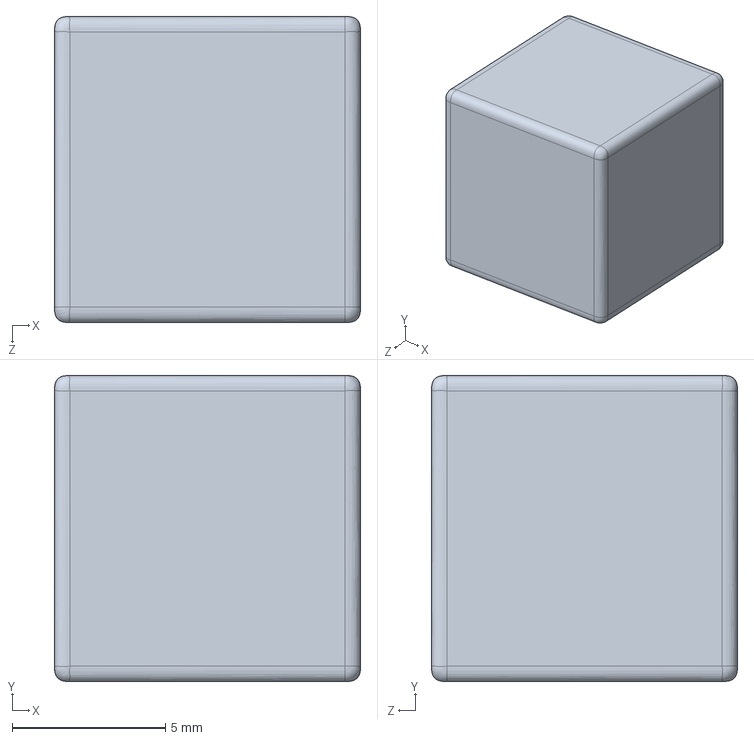
[picture p81: CAD file, 2024-10-25]
Mechanics/MAZE ROBOT 2024/Pista/Kit de Resgate.SLDPRT
10.0 x 10.0 x 10.0 mm
