franrobots/RescueMaze_FranRobots_National2024/Mechanics/MAZE ROBOT 2024/Rodas e esteiras/Dentes Esteira/Dente Esteira - Engrenagem.SLDPRT

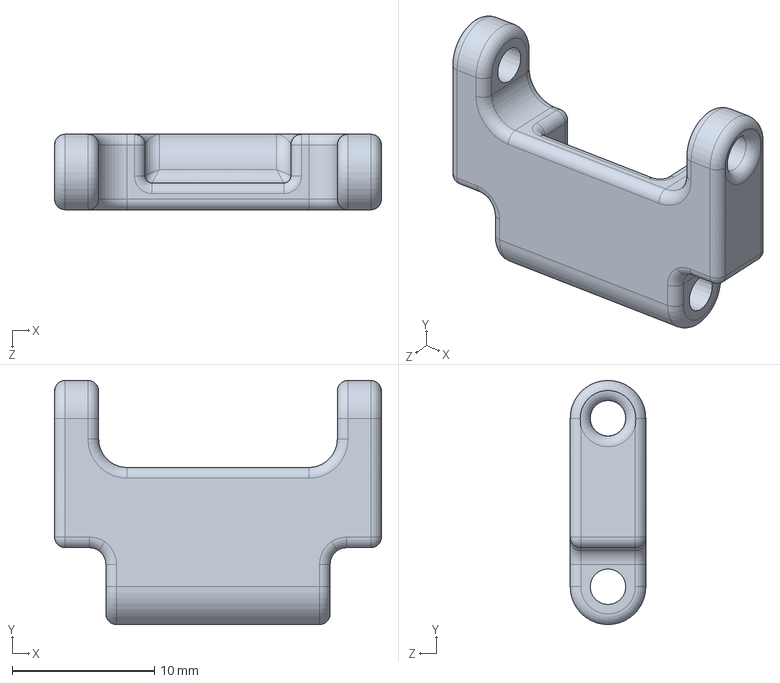
[picture p82: CAD file, 2024-10-25]
Mechanics/MAZE ROBOT 2024/Rodas e esteiras/Dentes Esteira/Dente Esteira - Engrenagem.SLDPRT
23.0 x 17.2 x 5.32 mm
