franrobots/RescueMaze_FranRobots_National2024/Mechanics/MAZE ROBOT 2024/Rodas e esteiras/Rodas/7988 - Atual/Engrenagem Mov. Red. Encoder - 11,92_7988.SLDPRT

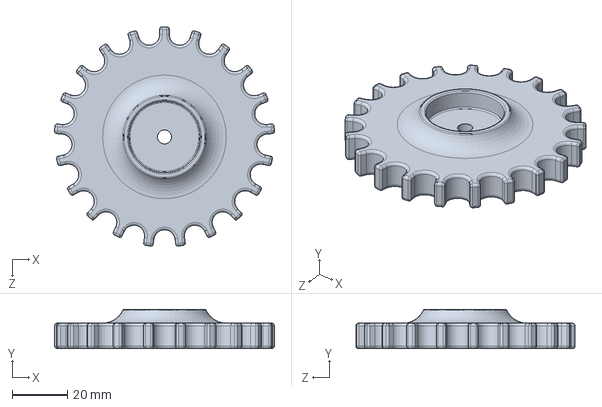
[picture p83: CAD file, 2024-10-25]
Mechanics/MAZE ROBOT 2024/Rodas e esteiras/Rodas/7988 - Atual/Engrenagem Mov. Red. Encoder - 11,92_7988.SLDPRT
79.8 x 14.2 x 79.6 mm
