franrobots/RescueMaze_FranRobots_National2024/Mechanics/MAZE ROBOT 2024/Componentes/Bateria/Bateria 2200mAh 11.1V Lion Power.SLDPRT

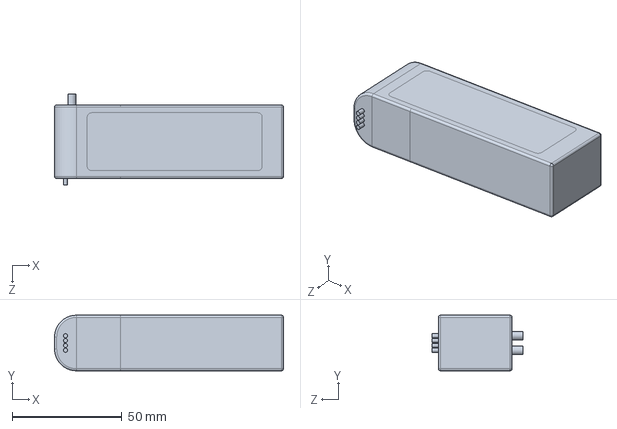
[picture p84: CAD file, 2024-10-25]
Mechanics/MAZE ROBOT 2024/Componentes/Bateria/Bateria 2200mAh 11.1V Lion Power.SLDPRT
104.4 x 25.4 x 41.6 mm
