franrobots/RescueMaze_FranRobots_National2024/Mechanics/MAZE ROBOT 2024/Componentes/Display Bateria MH-DL18S.SLDPRT

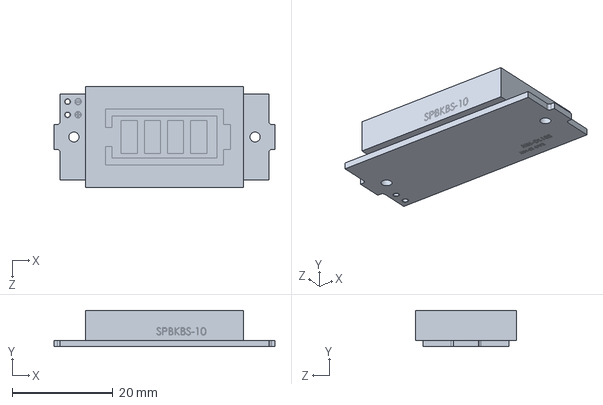
[picture p85: CAD file, 2024-10-25]
Mechanics/MAZE ROBOT 2024/Componentes/Display Bateria MH-DL18S.SLDPRT
43.8 x 7.20 x 20.0 mm
