franrobots/RescueMaze_FranRobots_National2024/Mechanics/MAZE ROBOT 2024/Componentes/GY-VL53/Adaptador GY_VL53 LDK-1XV2.SLDPRT

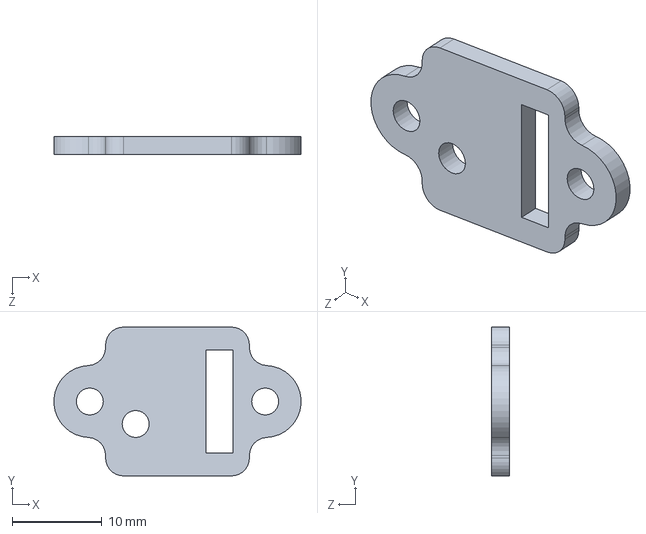
[picture p86: CAD file, 2024-10-25]
Mechanics/MAZE ROBOT 2024/Componentes/GY-VL53/Adaptador GY_VL53 LDK-1XV2.SLDPRT
27.5 x 16.6 x 2.00 mm
