franrobots/RescueMaze_FranRobots_National2024/Mechanics/MAZE ROBOT 2024/Componentes/Placa Mãe - Robô Maze/Conectores/Barras Pinada Fêmea/15-Pin Header - Female - 2.54mm.step

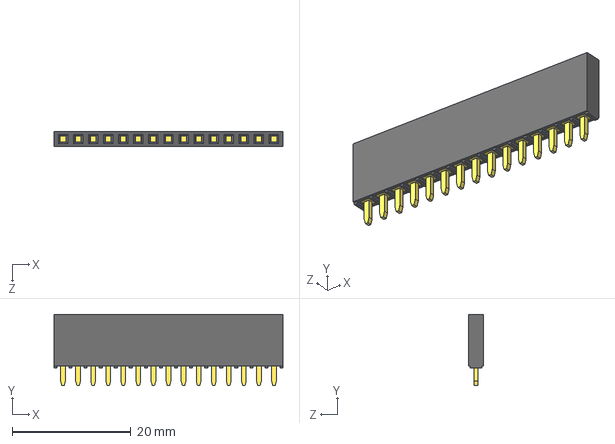
[picture p87: CAD file, 2024-10-25]
Mechanics/MAZE ROBOT 2024/Componentes/Placa Mãe - Robô Maze/Conectores/Barras Pinada Fêmea/15-Pin Header - Female - 2.54mm.step
38.6 x 12.0 x 2.50 mm
