franrobots/RescueMaze_FranRobots_National2024/Mechanics/MAZE ROBOT 2024/Componentes/Placa Mãe - Robô Maze/Conectores/Barras Pinada Macho/2-Pin Header - Male - 2.54mm.step

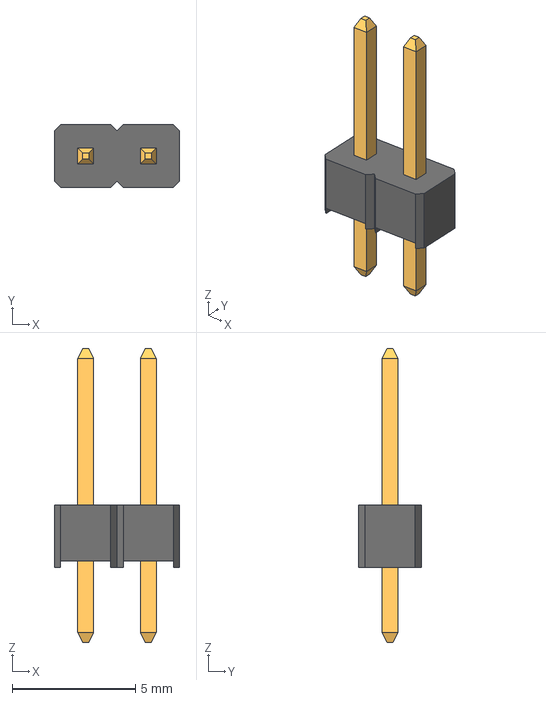
[picture p88: CAD file, 2024-10-25]
Mechanics/MAZE ROBOT 2024/Componentes/Placa Mãe - Robô Maze/Conectores/Barras Pinada Macho/2-Pin Header - Male - 2.54mm.step
5.08 x 2.54 x 11.9 mm
