franrobots/RescueMaze_FranRobots_National2024/Mechanics/MAZE ROBOT 2024/Componentes/Servo Motor/SG90 - Micro Servo 9g - Tower Pro.SLDPRT

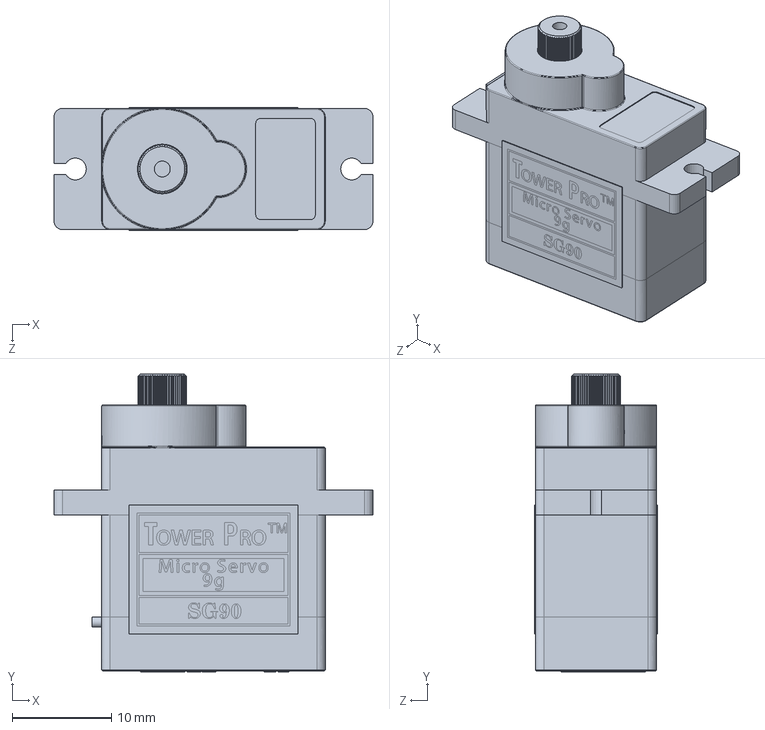
[picture p89: CAD file, 2024-10-25]
Mechanics/MAZE ROBOT 2024/Componentes/Servo Motor/SG90 - Micro Servo 9g - Tower Pro.SLDPRT
32.1 x 30.0 x 12.4 mm
