franrobots/RescueMaze_FranRobots_National2024/Mechanics/MAZE ROBOT 2024/Componentes/Switchs/Microswitch KW11-3Z-3.SLDPRT

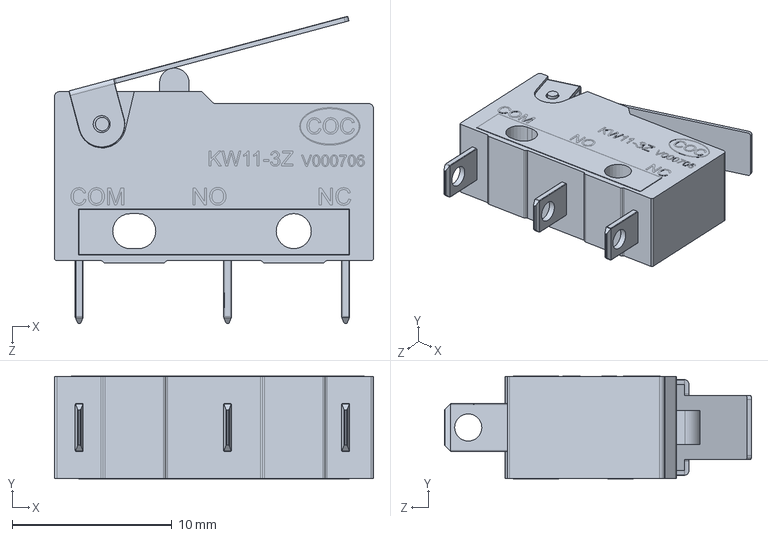
[picture p90: CAD file, 2024-10-25]
Mechanics/MAZE ROBOT 2024/Componentes/Switchs/Microswitch KW11-3Z-3.SLDPRT
20.0 x 6.44 x 19.3 mm
