franrobots/RescueMaze_FranRobots_National2024/Mechanics/MAZE ROBOT 2024/Componentes/Ultrassonico/Ultrassonico HC-SR04.SLDPRT

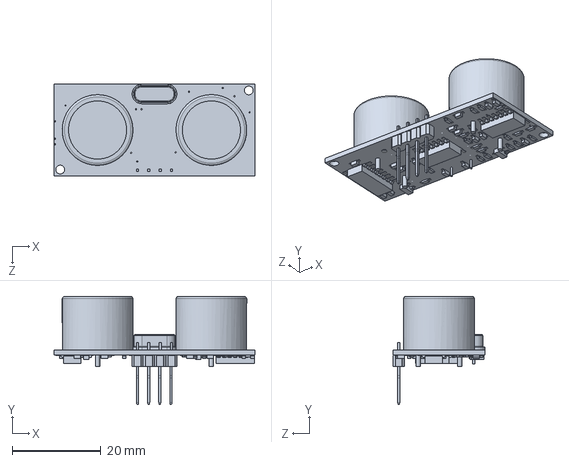
[picture p91: CAD file, 2024-10-25]
Mechanics/MAZE ROBOT 2024/Componentes/Ultrassonico/Ultrassonico HC-SR04.SLDPRT
45.2 x 24.3 x 20.6 mm
