franrobots/RescueMaze_FranRobots_National2024/Mechanics/MAZE ROBOT 2024/Disparador/Disparador Tapete/Émbolo Tapete Disparador.SLDPRT

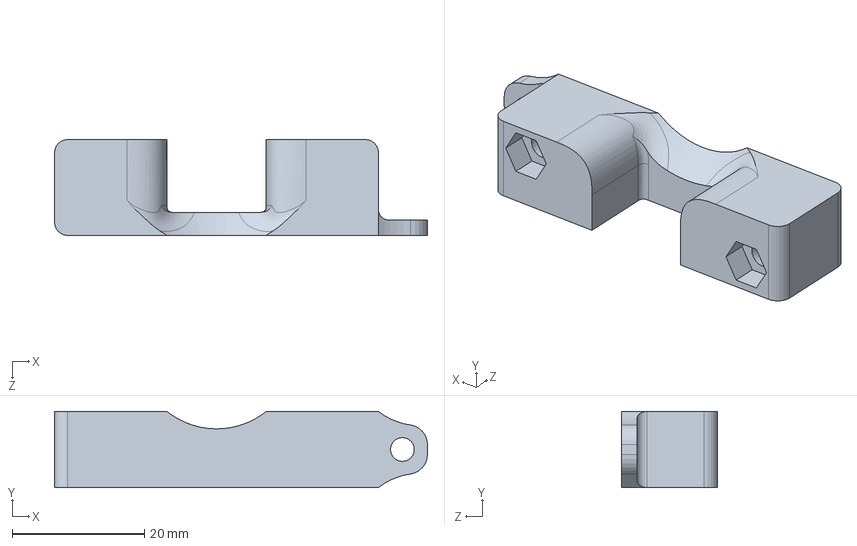
[picture p92: CAD file, 2024-10-25]
Mechanics/MAZE ROBOT 2024/Disparador/Disparador Tapete/Émbolo Tapete Disparador.SLDPRT
56.4 x 11.5 x 14.5 mm
