franrobots/RescueMaze_FranRobots_National2024/Mechanics/MAZE ROBOT 2024/Lateral Esquerda Botão - Maze.SLDPRT

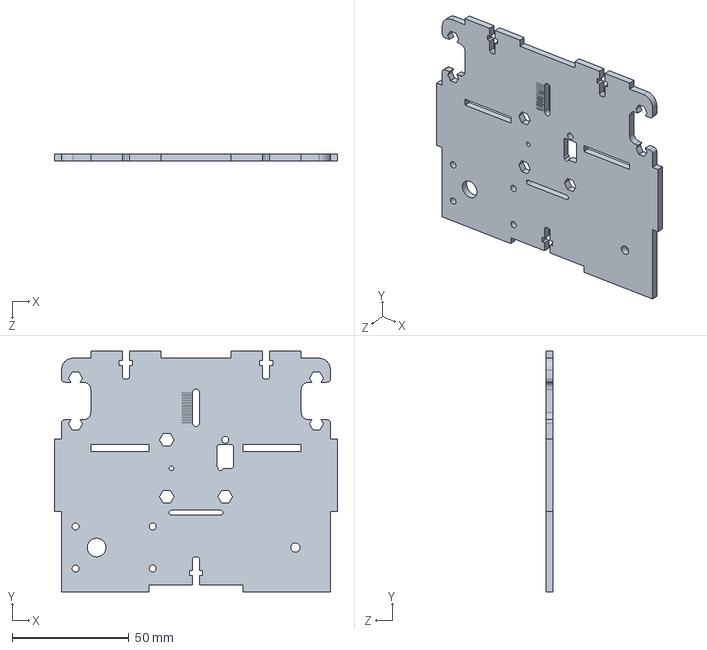
[picture p94: CAD file, 2024-10-25]
Mechanics/MAZE ROBOT 2024/Lateral Esquerda Botão - Maze.SLDPRT
121.0 x 103.0 x 3.00 mm
