franrobots/RescueMaze_FranRobots_National2024/Mechanics/MAZE ROBOT 2024/Rodas e esteiras/Dentes Esteira/Eixo Junção Esteira.SLDPRT

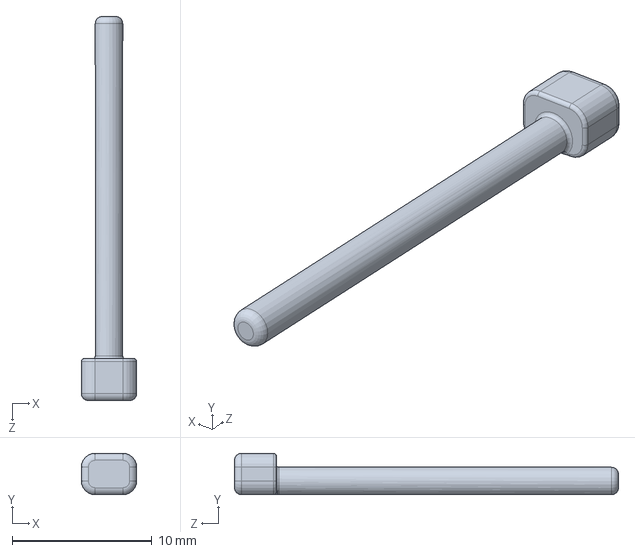
[picture p96: CAD file, 2024-10-25]
Mechanics/MAZE ROBOT 2024/Rodas e esteiras/Dentes Esteira/Eixo Junção Esteira.SLDPRT
3.97 x 2.97 x 27.5 mm
