franrobots/RescueMaze_FranRobots_National2024/Mechanics/MAZE ROBOT 2024/Rodas e esteiras/Rodas/7988 - Atual/Engrenagem Movida Reduzida - Passo 11,92 7988.SLDPRT

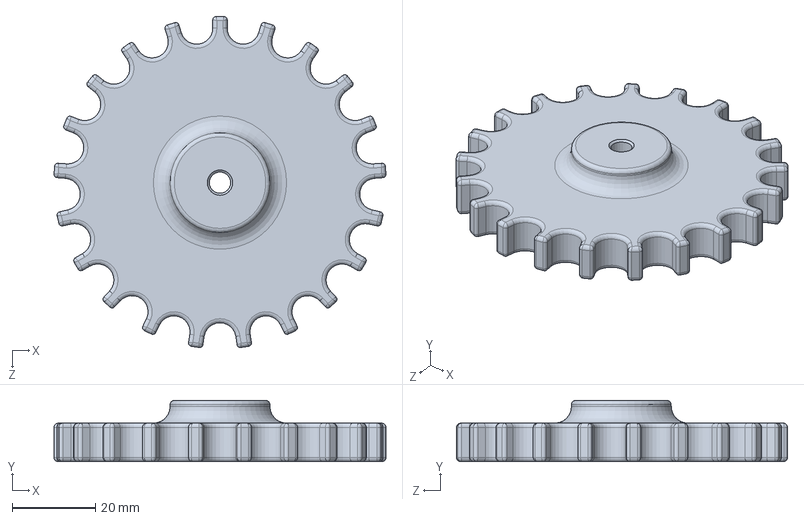
[picture p97: CAD file, 2024-10-25]
Mechanics/MAZE ROBOT 2024/Rodas e esteiras/Rodas/7988 - Atual/Engrenagem Movida Reduzida - Passo 11,92 7988.SLDPRT
79.8 x 14.7 x 79.6 mm
