franrobots/RescueMaze_FranRobots_National2024/Mechanics/MAZE ROBOT 2024/Componentes/GY-VL53/GY-VL53L1XV2.SLDPRT

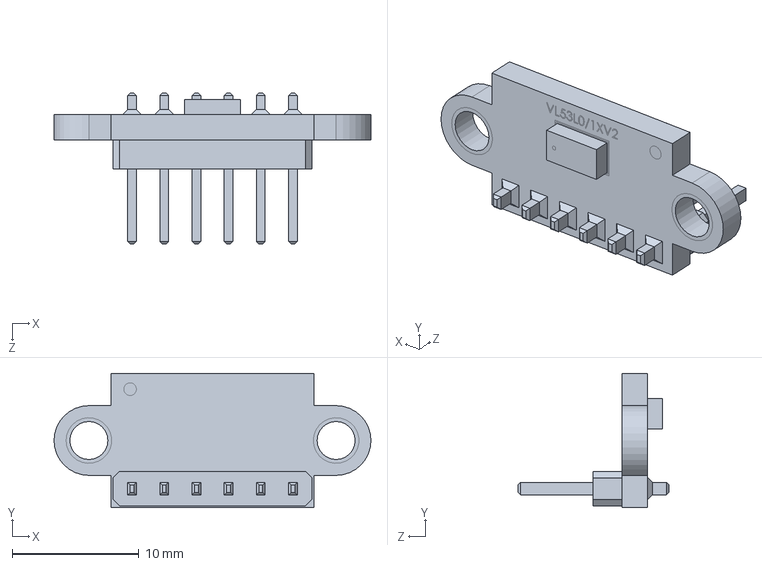
[picture p98: CAD file, 2024-10-25]
Mechanics/MAZE ROBOT 2024/Componentes/GY-VL53/GY-VL53L1XV2.SLDPRT
25.0 x 10.6 x 11.9 mm
