franrobots/RescueMaze_FranRobots_National2024/Mechanics/MAZE ROBOT 2024/Componentes/Placa de Refletância/Case LDR Dupla.SLDPRT

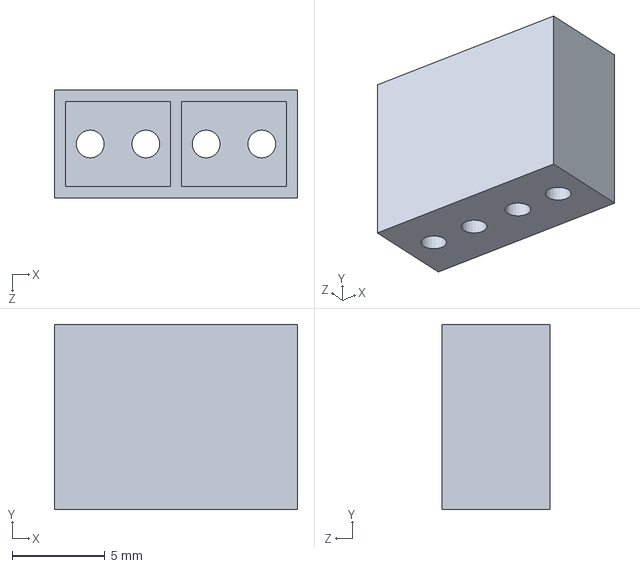
[picture p99: CAD file, 2024-10-25]
Mechanics/MAZE ROBOT 2024/Componentes/Placa de Refletância/Case LDR Dupla.SLDPRT
13.1 x 10.0 x 5.80 mm
