franrobots/RescueMaze_FranRobots_National2024/Mechanics/MAZE ROBOT 2024/Disparador/Disparador Tapete/Parede Inclinada - Disparador.SLDPRT

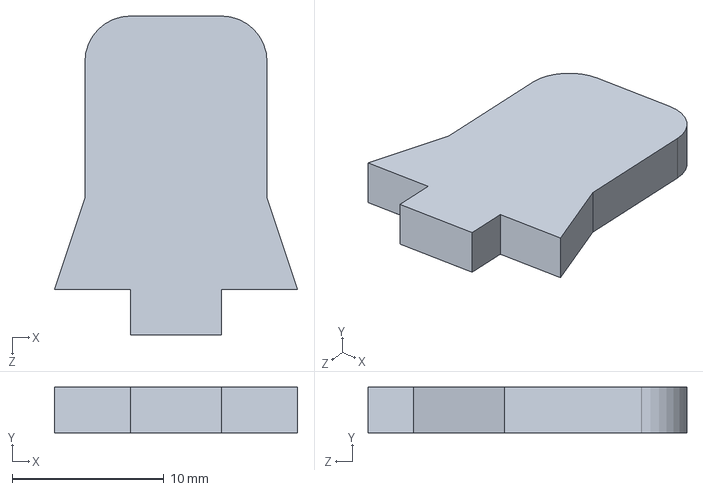
[picture p100: CAD file, 2024-10-25]
Mechanics/MAZE ROBOT 2024/Disparador/Disparador Tapete/Parede Inclinada - Disparador.SLDPRT
16.0 x 3.00 x 21.0 mm
