franrobots/RescueMaze_FranRobots_National2024/Mechanics/MAZE ROBOT 2024/Disparador/Estoque Disparador/Tampa Superior - Estoque Disparador.SLDPRT

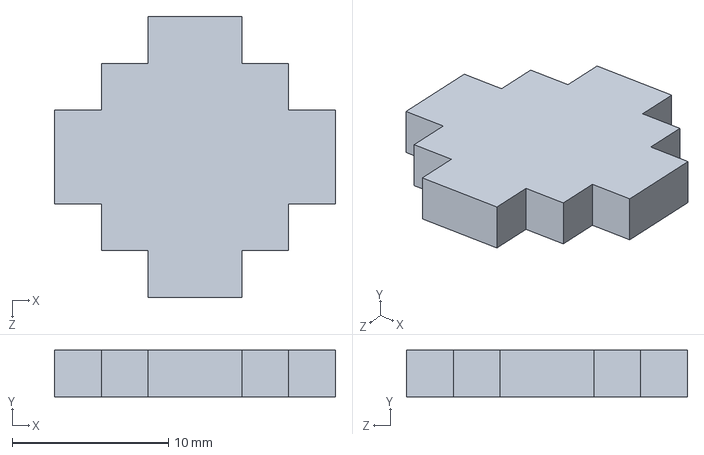
[picture p101: CAD file, 2024-10-25]
Mechanics/MAZE ROBOT 2024/Disparador/Estoque Disparador/Tampa Superior - Estoque Disparador.SLDPRT
18.0 x 3.00 x 18.0 mm
