franrobots/RescueMaze_FranRobots_National2024/Mechanics/MAZE ROBOT 2024/Alça Robô Maze.SLDPRT

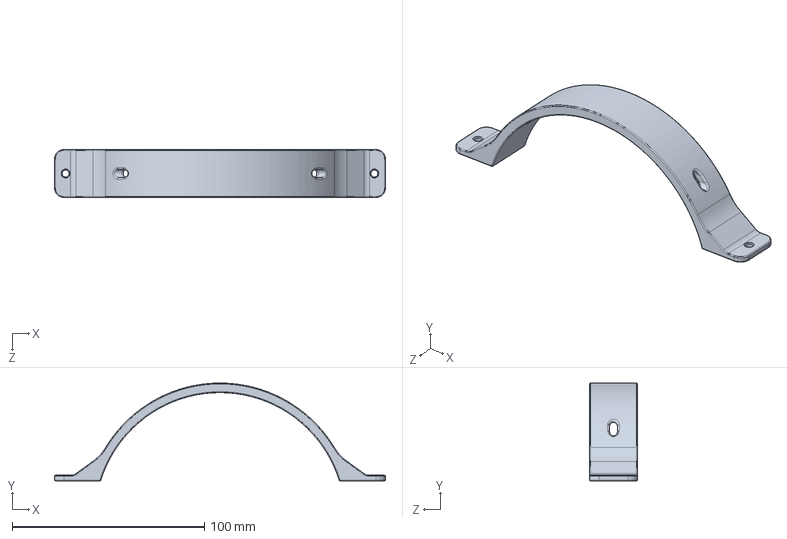
[picture p102: CAD file, 2024-10-25]
Mechanics/MAZE ROBOT 2024/Alça Robô Maze.SLDPRT
172.3 x 51.0 x 25.0 mm
