franrobots/RescueMaze_FranRobots_National2024/Mechanics/MAZE ROBOT 2024/Disparador/Disparador Tapete/Eixo Biela.SLDPRT

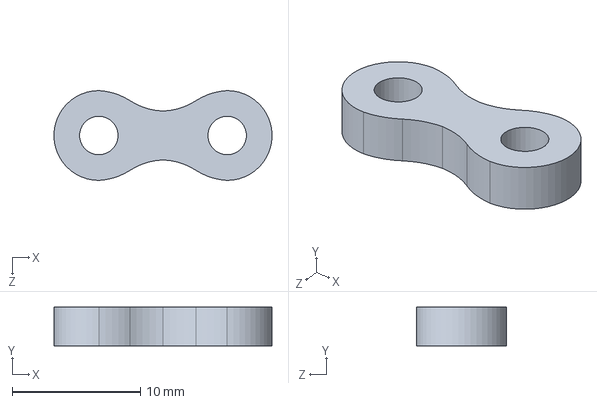
[picture p103: CAD file, 2024-10-25]
Mechanics/MAZE ROBOT 2024/Disparador/Disparador Tapete/Eixo Biela.SLDPRT
17.0 x 3.00 x 7.00 mm
