franrobots/RescueMaze_FranRobots_National2024/Mechanics/MAZE ROBOT 2024/Disparador/Estoque Disparador/Tampa - Estoque Disparador.SLDPRT

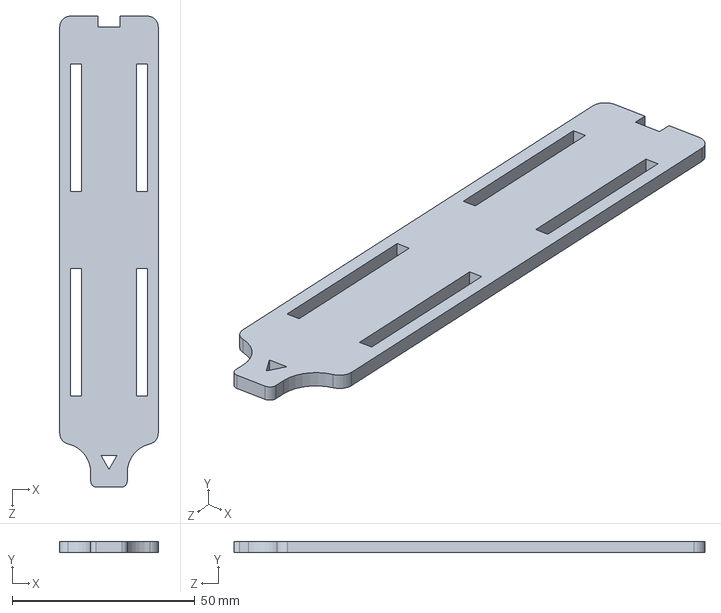
[picture p104: CAD file, 2024-10-25]
Mechanics/MAZE ROBOT 2024/Disparador/Estoque Disparador/Tampa - Estoque Disparador.SLDPRT
27.0 x 3.00 x 129.0 mm
