franrobots/RescueMaze_FranRobots_National2024/Mechanics/MAZE ROBOT 2024/Andar Base - Maze.SLDPRT

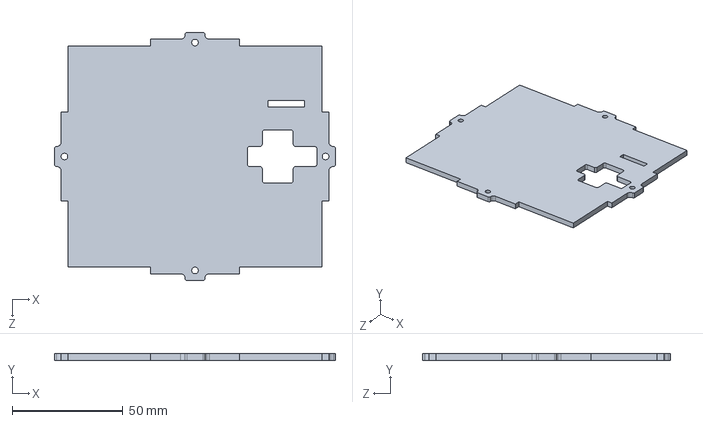
[picture p105: CAD file, 2024-10-25]
Mechanics/MAZE ROBOT 2024/Andar Base - Maze.SLDPRT
127.0 x 3.00 x 112.0 mm
