franrobots/RescueMaze_FranRobots_National2024/Mechanics/MAZE ROBOT 2024/Teto - Robô Maze.SLDPRT

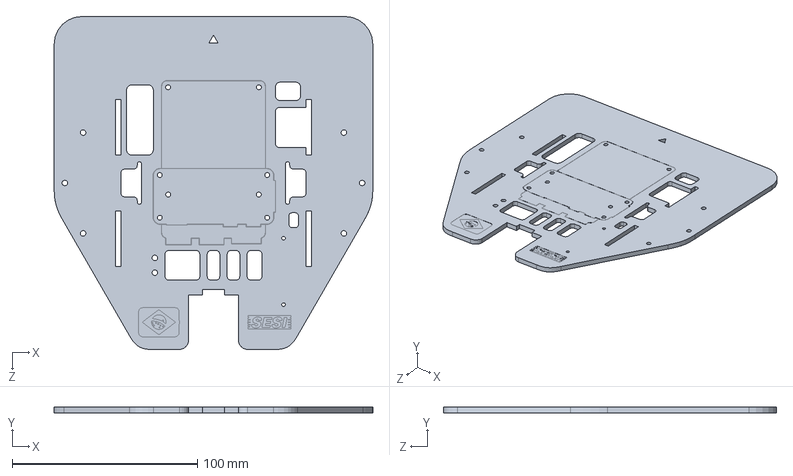
[picture p107: CAD file, 2024-10-25]
Mechanics/MAZE ROBOT 2024/Teto - Robô Maze.SLDPRT
172.3 x 3.00 x 180.0 mm
