franrobots/RescueMaze_FranRobots_National2024/Mechanics/MAZE ROBOT 2024/Peça Trás - Maze.SLDPRT

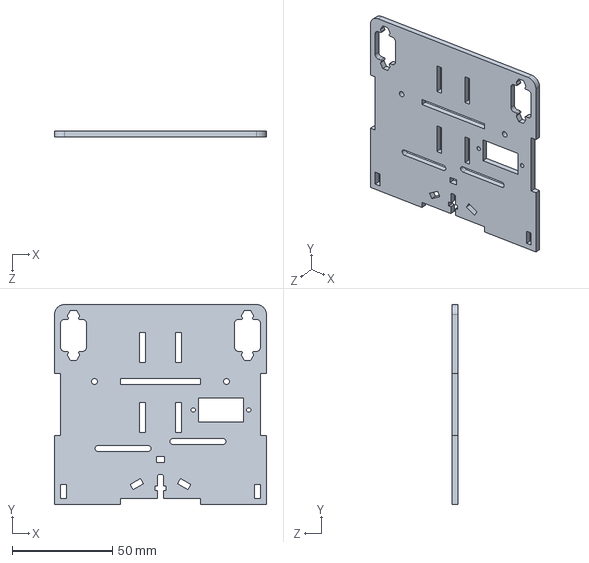
[picture p108: CAD file, 2024-10-25]
Mechanics/MAZE ROBOT 2024/Peça Trás - Maze.SLDPRT
106.0 x 100.0 x 3.00 mm
